alnhan/WearableAlertDevice/Documentation/WAR Feb 22nd-28th.pdf

Executive Summary: This week our team finalized our beginning information for our PDR. We

finished our presentation by completing all required charts, block diagrams, and plans. Our

presentation has been practiced as is ready to go for Monday 3/02. For next week our team will

begin working on schematics and the technical side of our project. At the end of next week we

will have the parts ordered for our project and the schematics done for when the parts arrive. The

software will be continued to be worked on so that we may be completely ready for testing when

the project is finished building.

Hardware:

Cody C.
Progress:
- Found Arduino Nano ESP32 schematics (~ 5 minutes)
- Create block diagram for gunshot detection (~1 hour 30 minutes)
- Presentation:
- Created slides and researched for PDR (~ 4 hours)

■ Created rough script and bullet points on what I need to cover

- Going in detail onto the I2S MEMS microphone, explaining the

functions, restrictions, and how we plan to overcome the

limitations of 140 dB

- Practice PDR presentation individually (~ 30 minutes)
- 2/28 – Weekly meeting with the team (~ 3 hours)
- Finalize what components and features we want to use for the wearable alert

device (Prioritize functionality over portability)

■ Boost converter, power supply

- Practice presentation with the group

■ Muting at correct times, coordinating who will say what information and

at which slides.

Total Hours Worked: ~ 9 Hours 5 Minutes

Future Work/Plan

- 3/2 - Preliminary Design Review (Presentation)
- Finalize order of parts for the gunshot detection and for overall project
- Create schematics for all components
- Reorganize Arduino Nano ESP32 schematics
- Create rough schematics of all required components for the gunshot detection

:

Hardware:

Ryan K.
Progress:
- 2/25 (2hrs)
- Created and worked on hardware specific slides for the PDR
- Created block diagram for the positioning module
- Practiced presenting PDR slides individually
- 2/28 (3hrs)
- Attended team meeting where we discussed and finalized the PDR presentation
- Practice presenting the PDR slides as a group

Total Hours Worked: 5hrs

Future Work/Plan:

- Deliver PDR presentation Monday (3/2)
- Coordinate with team on what all needs to be ordered for the project
- Create schematics for all components

Software:

Alex H.
Progress:

Total Hours Worked:

- 2/24 (1 h 27 min)
- Continued working on PDR slides
- Finished introduction slide for PDR
- Finished audio processing software block diagram
- 2/27 (3 h 52 min)
- Completed PDR slides
- Finished overall software block diagram
- Practiced presenting software slides of PDR
- 2/28 (2 h)
- Practiced entire PDR presentation with the rest of the team

Future Work/Plan:

- Deliver PDR presentation Monday (3/2) night
- Start writing software for device

Project Manager:

Jonas W.

Progress:

- 2/24 (30 min)
- Began work on PDR slides
- Finished introduction slide for PDR
- 2/27 (1 hr)
- Finished my PDR slides
- Finished block diagrams and budget plan
- Finished Datasheet booklet
- 2/28 (2 h)
- Practiced entire PDR presentation with the rest of the team
- Finalized PDR with charts and information

Total Hours Worked: 3 hr 30 min

Future Work/Plan:

- Deliver PDR
- Order parts for circuit
- Finish schematics for hardware and begin slides for CDR
