alnhan/WearableAlertDevice/Presentations/CCEW PDR.pdf

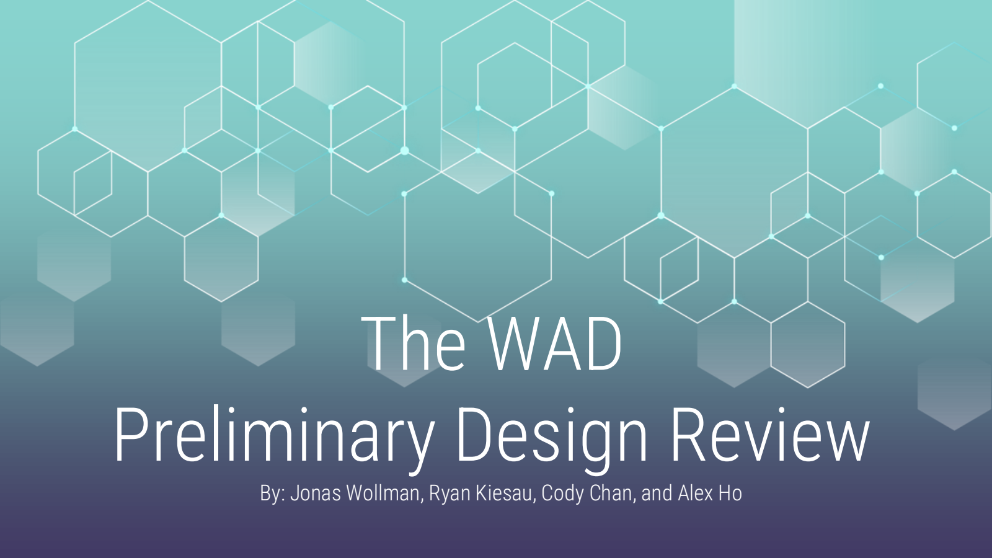
[picture p57: page 1]

# The WAD Preliminary Design Review

By: Jonas Wollman, Ryan Kiesau, Cody Chan, and Alex Ho

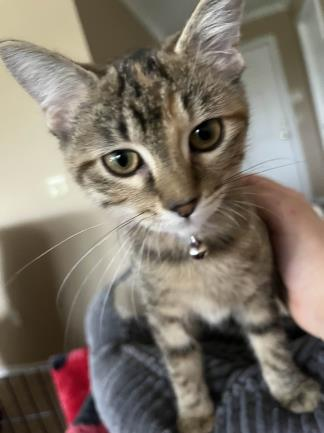
[picture p58: figure]

# Introductions

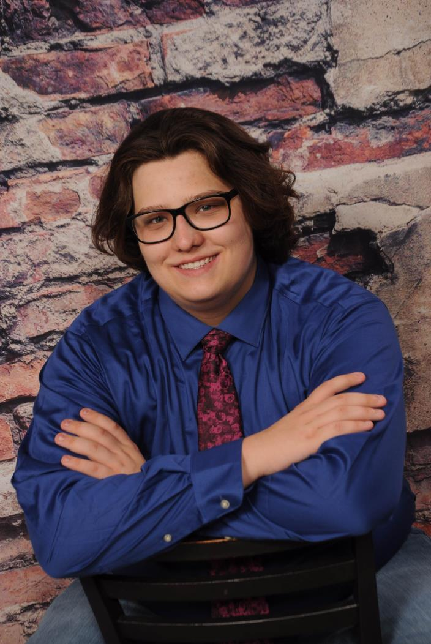
[picture p59: figure]

### Name: Jonas Wollman

### Major: Computer Engineering

### Role: Project Manager

### Post-College Plans: Working as an electronics engineer for the 76th Software Engineering Group (555th Squadron) at Tinker Air Force Base

JW

RK

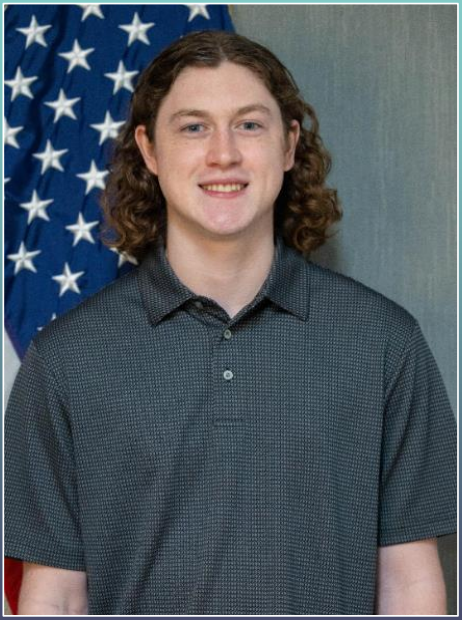
[picture p60: figure]

### Name: Ryan Kiesau

### Major: Electrical Engineering

### Role: Hardware

### Post-College Plans: Working as an electronics engineer for the 76th Software Engineering Group (557th Squadron) at Tinker Air Force Base

# Introductions

CC

# Introductions

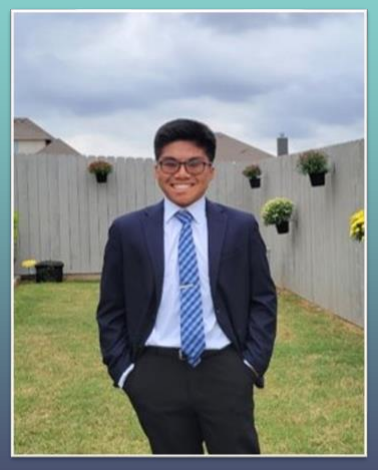
[picture p61: figure]

### Name: Cody Chan

### Major: Computer Engineering

### Role: Hardware

### Post-College Plans: Pursue Master’s in Electrical Engineering -The University of Oklahoma

AH

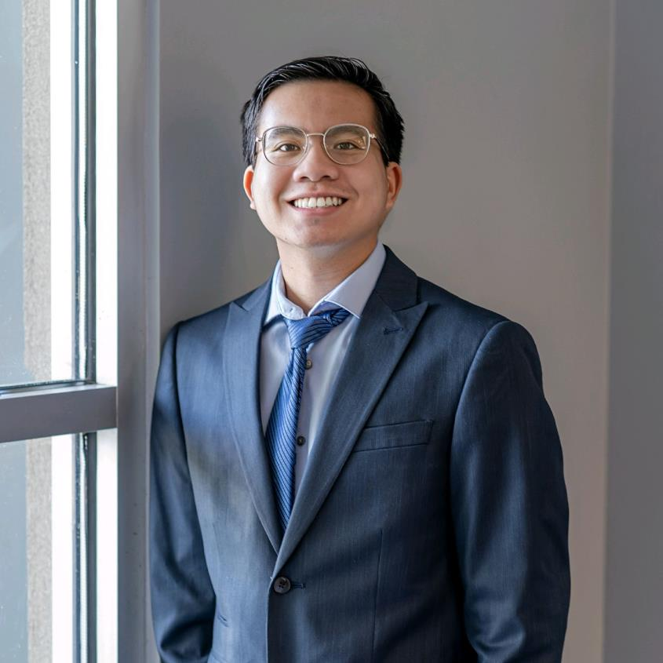
[picture p62: figure]

Name: Alex Ho

Major: Computer Engineering

Graduation Date: May 2026

Role: Software

Post-College Plans: Working as an electronics engineer at Tinker Air Force Base

# Introductions

# Problem & Plan

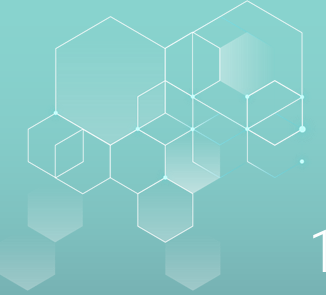
[picture p63: figure]
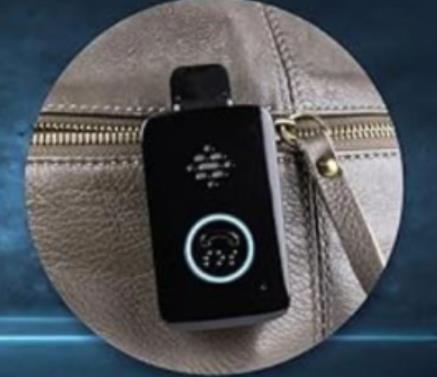
[picture p64: figure]

# 1. Wearability

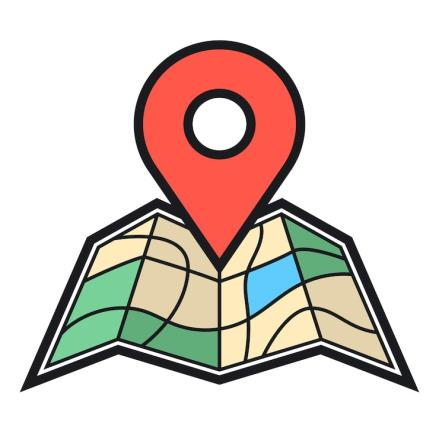
[picture p65: figure]

# 2. Functionality

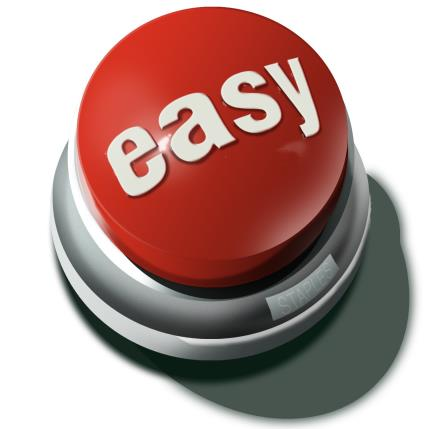
[picture p66: figure]

# 3. Ease of Use

JW

# Problem & Plan

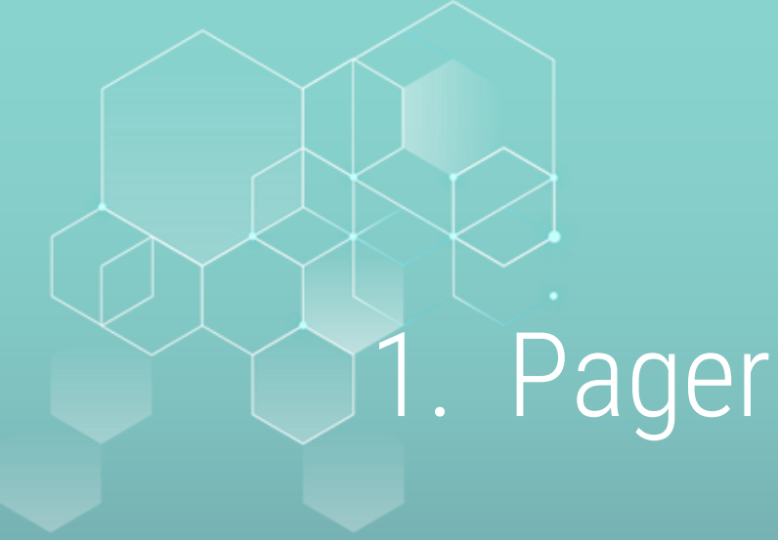
[picture p67: figure]
1. Pager
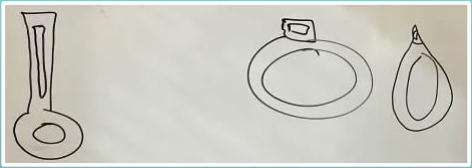
[picture p68: figure]

# 2. Gunshot & GPS

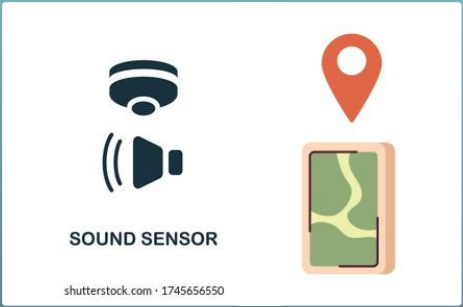
[picture p69: figure]
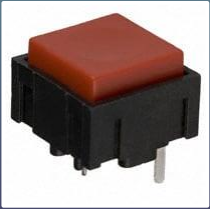
[picture p70: figure]

# 3. Click of a Button

JW

# Overview Block Diagram

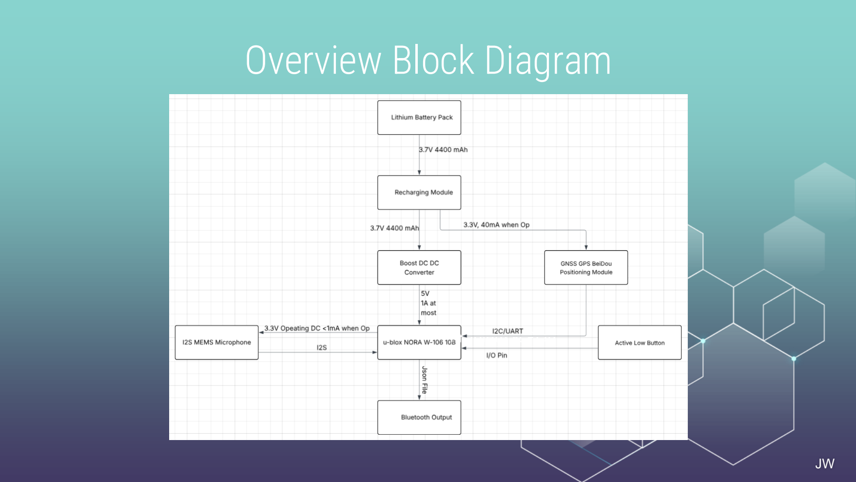
[picture p71: page 8]

JW

# Hardware System Overview

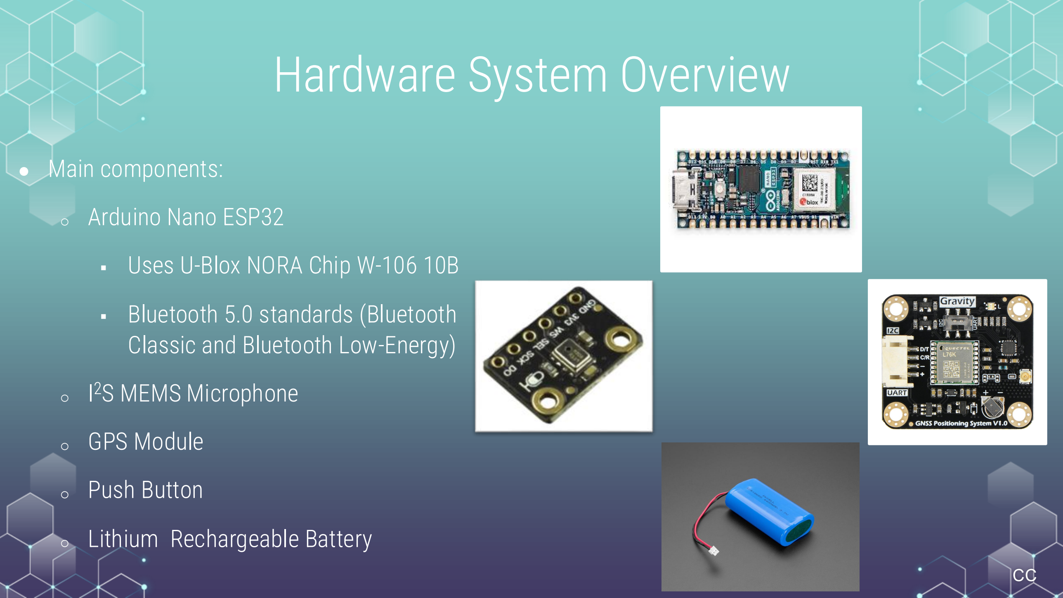
[picture p72: page 9]

- Main components:
- Arduino Nano ESP32
- Uses U-Blox NORA Chip W-106 10B
- Bluetooth 5.0 standards (Bluetooth Classic and Bluetooth Low-Energy)
- I

2S MEMS Microphone

- GPS Module
- Push Button
- Lithium Rechargeable Battery

CC

# Audio Sampling Block Diagram

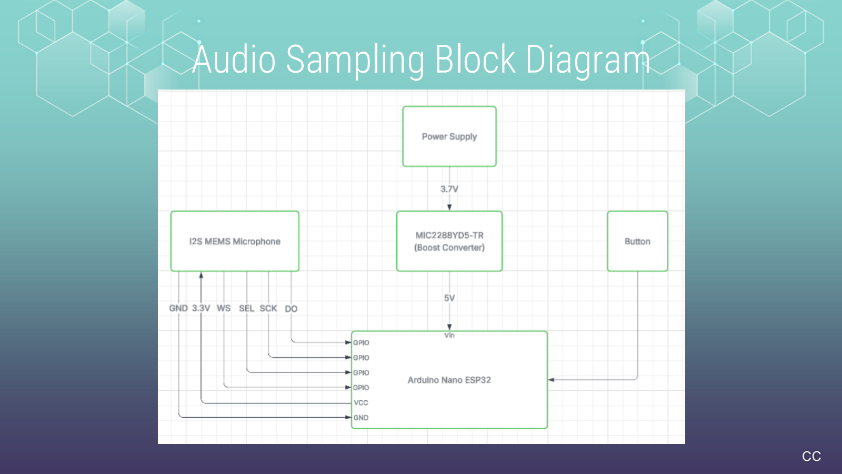
[picture p73: page 10]

CC

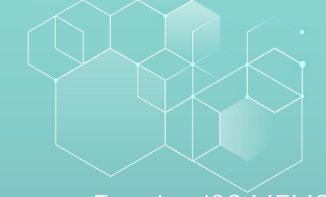
[picture p74: figure]
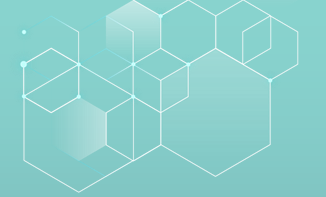
[picture p75: figure]

- Fermion I2S MEMS Microphone
- Operating Voltage: 3.3V
- Low Current: < 1mA
- Sound Pressure Level: 140 dB
- Signal-to-Noise Ratio: 59 dB
- Supports I²S

CC

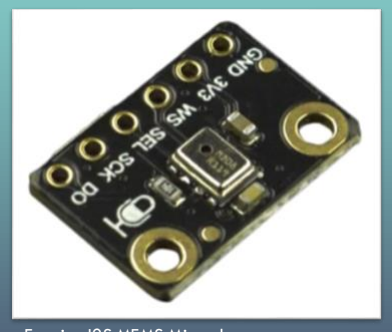
[picture p76: figure]

Fermion I2S MEMS Microphone

# Microphone Hardware

# Positioning Block Diagram

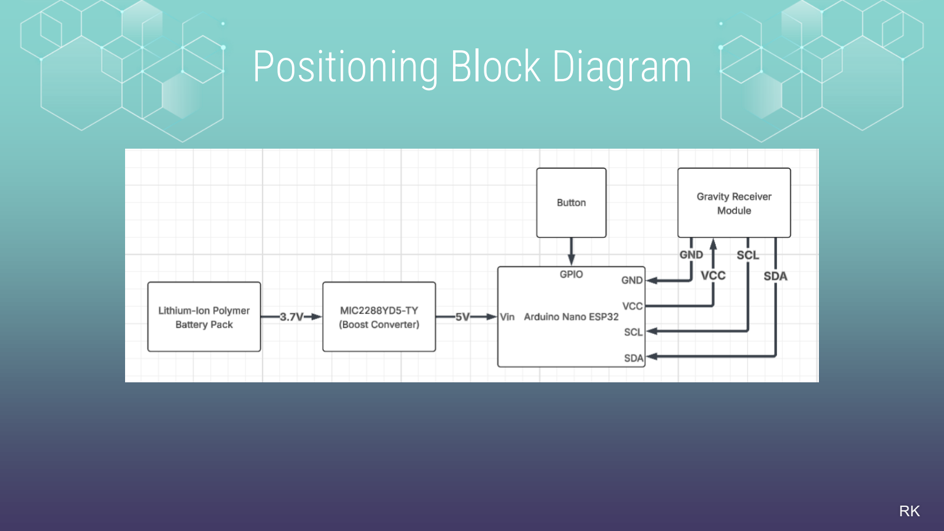
[picture p77: page 12]

RK

# Positioning Hardware

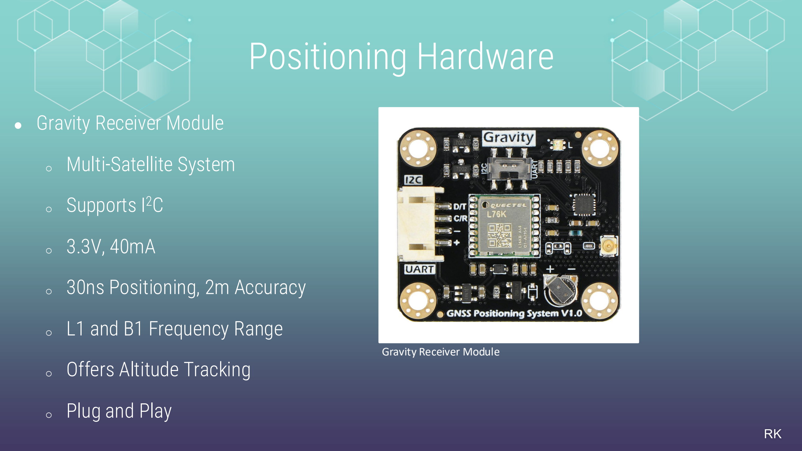
[picture p78: page 13]

- Gravity Receiver Module
- Multi-Satellite System
- Supports I²C
- 3.3V, 40mA
- 30ns Positioning, 2m Accuracy
- L1 and B1 Frequency Range
- Offers Altitude Tracking
- Plug and Play

Gravity Receiver Module

RK

# Power Supply

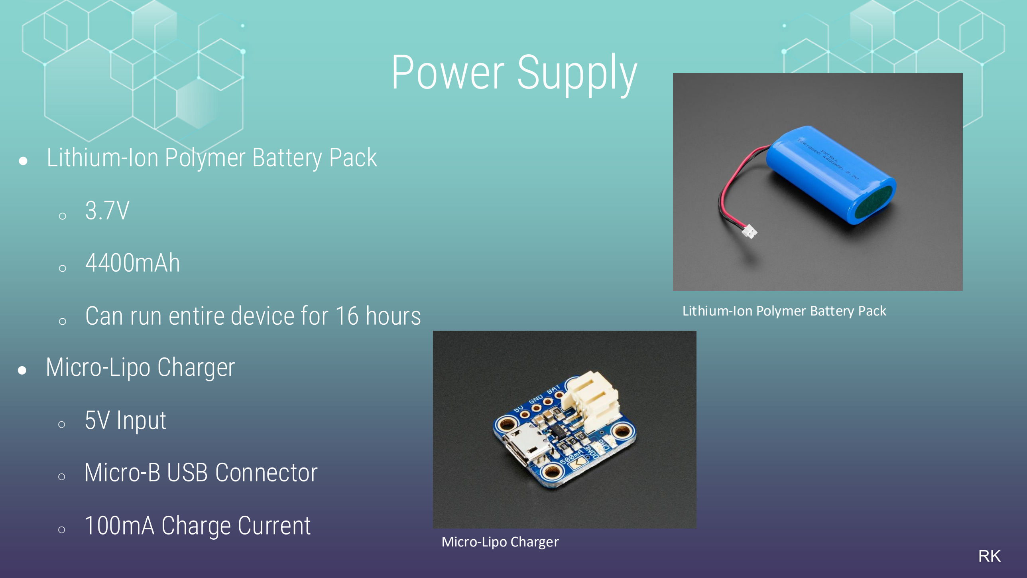
[picture p79: page 14]

- Lithium-Ion Polymer Battery Pack
- 3.7V
- 4400mAh
- Can run entire device for 16 hours

RK

Lithium-Ion Polymer Battery Pack

Micro-Lipo Charger

- Micro-Lipo Charger
- 5V Input
- Micro-B USB Connector
- 100mA Charge Current

Overview of Implementation

Programming Language: C++11 (follows joint technical standard ISO¹

/IEC² 14882)

Main Functionality:
1. Collect audio samples and process to find gunshots
2. Collect GPS data
3. Package data and transmit to mobile app

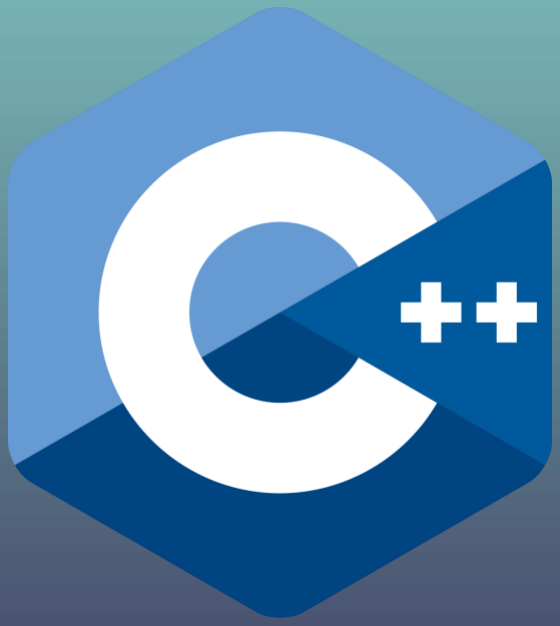
[picture p80: figure]

1. ISO – International Organization for Standardization | AH
2. IEC – International Electrotechnical Commission

# Software Design

Audio Signal Collection
- Data received from microphone in digital PCM¹ format
- I

2S protocol to sample audio from microphone
- Sampling Rate: 44.1 kHz

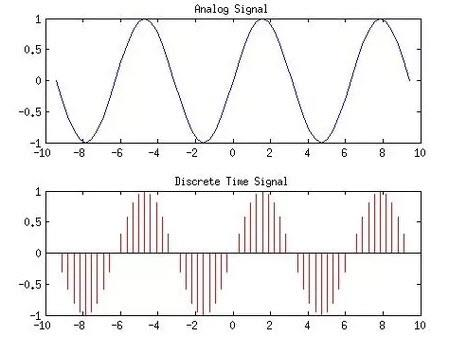
[picture p81: figure]

- Standard frequency for recreating audio signal with the same quality
- ESP32 supports sampling PCM¹ audio at up to 100 kHz
- ESP32 has enough memory to hold large set of audio data (512 KB of SRAM memory)

AH

# Software Design

### 1. PCM - Pulse-Code Modulation

Audio Signal Processing
- Analyzing audio sample with respect to frequency rather than time gives more information on gunshot audio patterns
- Software Library: arduinoFFT by @kosme on GitHub
- Aiming for at least 75% accuracy with gunshot detection

AH

# Signal Processing Design

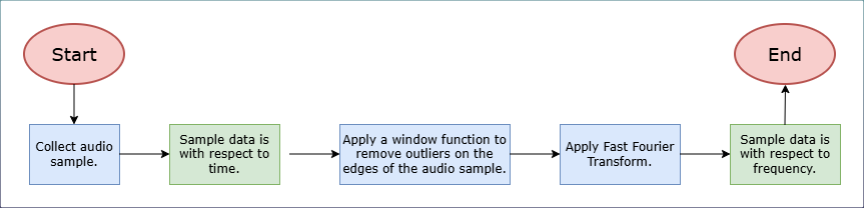
[picture p82: figure]

GPS Data Processing

- Obtains GPS data using I²C (Inter-Integrated Circuit) protocol
- Sampling Rate: 1 Hz

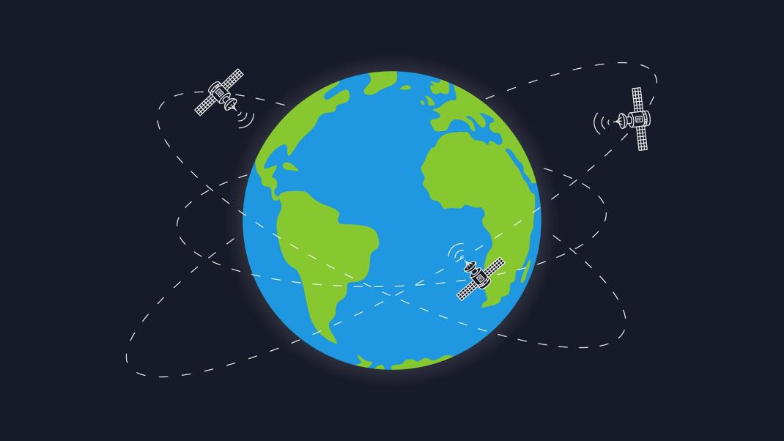
[picture p83: figure]

Collected Data:

1. Timestamp (CST)
2. Latitude (degrees)
3. Longitude (degrees)

AH

# GPS Data Processing

Wireless Data Transmission
- Audio and GPS data will be packaged together in JSON file and transmitted via Bluetooth Low-Energy (BLE)

Testing:
- Since mobile app is not functional yet, data will be transmitted to a completely

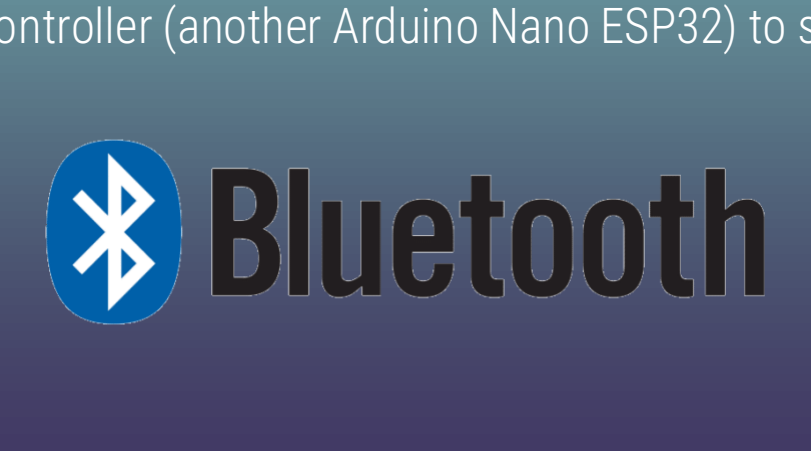
[picture p84: figure]

different microcontroller (another Arduino Nano ESP32) to see if transmission is successful

AH

# Bluetooth Design

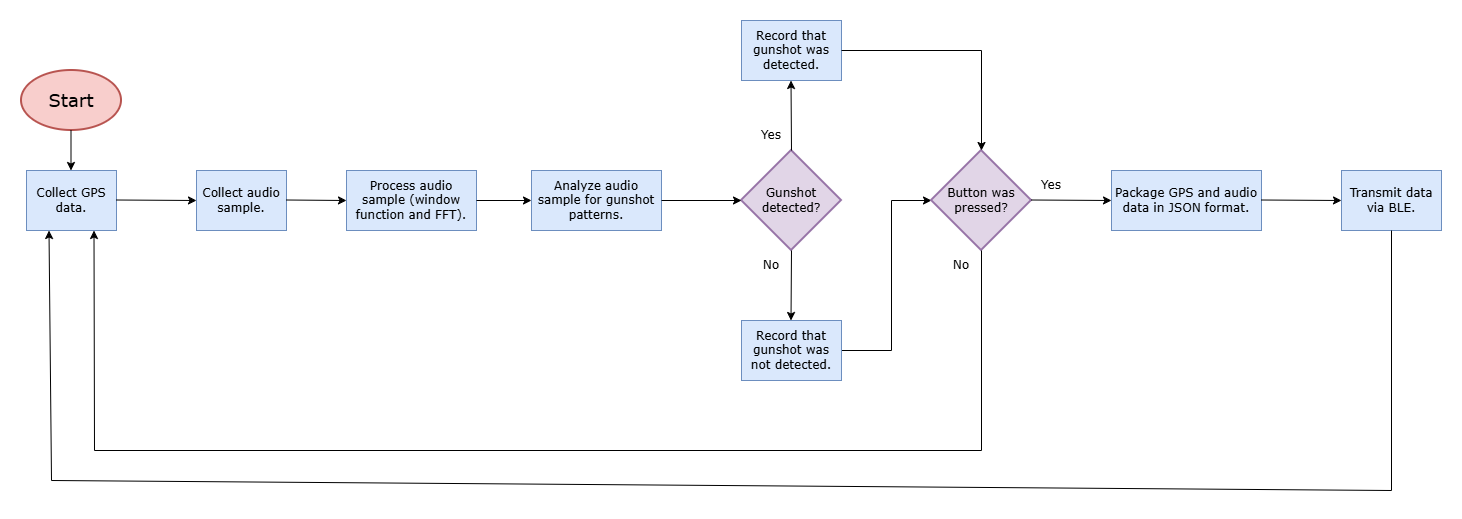
[picture p85: figure]

AH

# Software Block Diagram

# Budget Plan

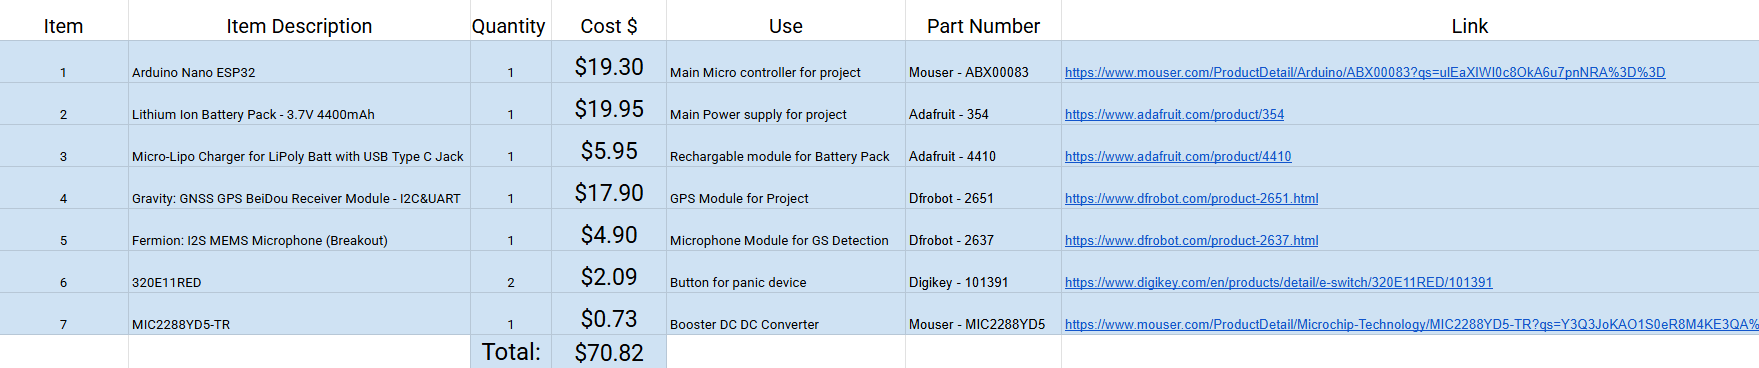
[picture p86: figure]

JW

JW

# Upcoming Plans

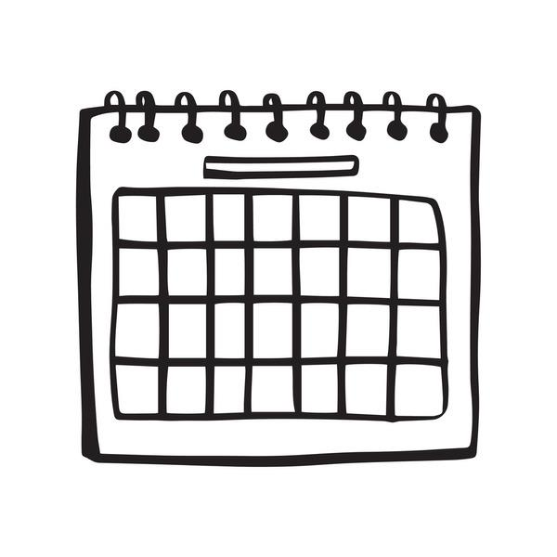
[picture p87: figure]

1-2 Weeks from Today:

-Ordering Parts & Creation of Schematics

2-4 Weeks from Today:

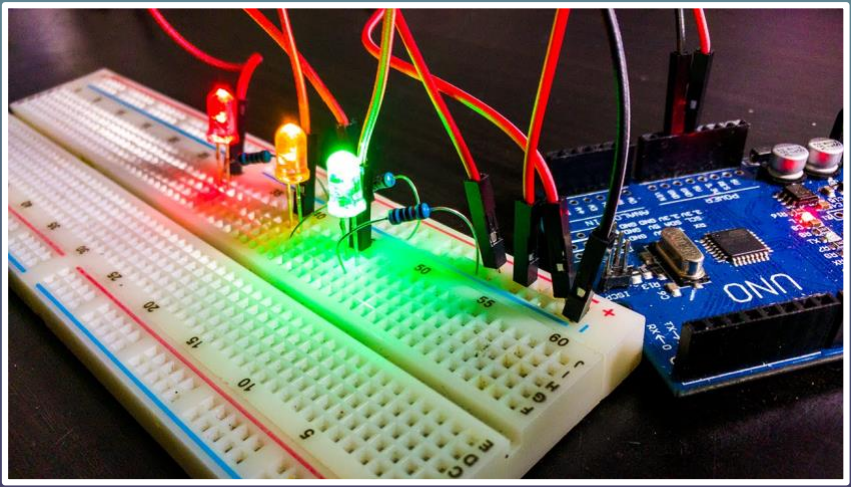
[picture p88: figure]

-Building of Board & Debugging

4-8 Weeks from Today:

-Testing & Future Planning

# Questions?
