alnhan/WearableAlertDevice/Documentation/Testing Images/20260425_123621.jpg

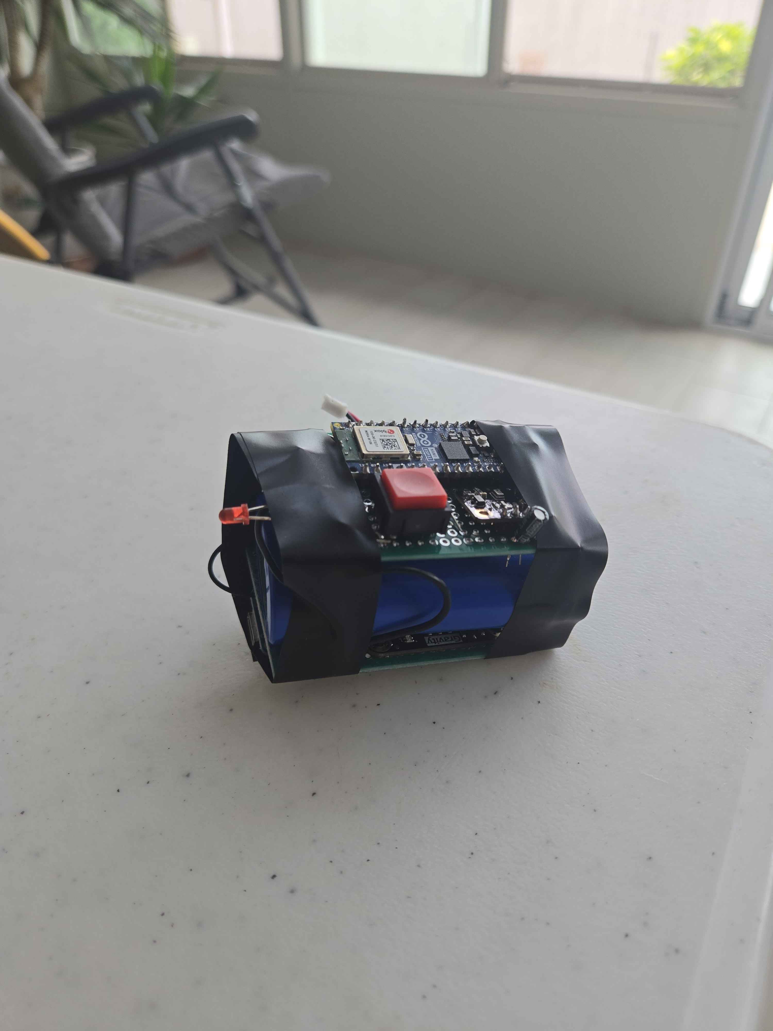
Documentation/Testing Images/20260425_123621.jpg
