alnhan/WearableAlertDevice/Documentation/Testing Images/20260425_123703.jpg

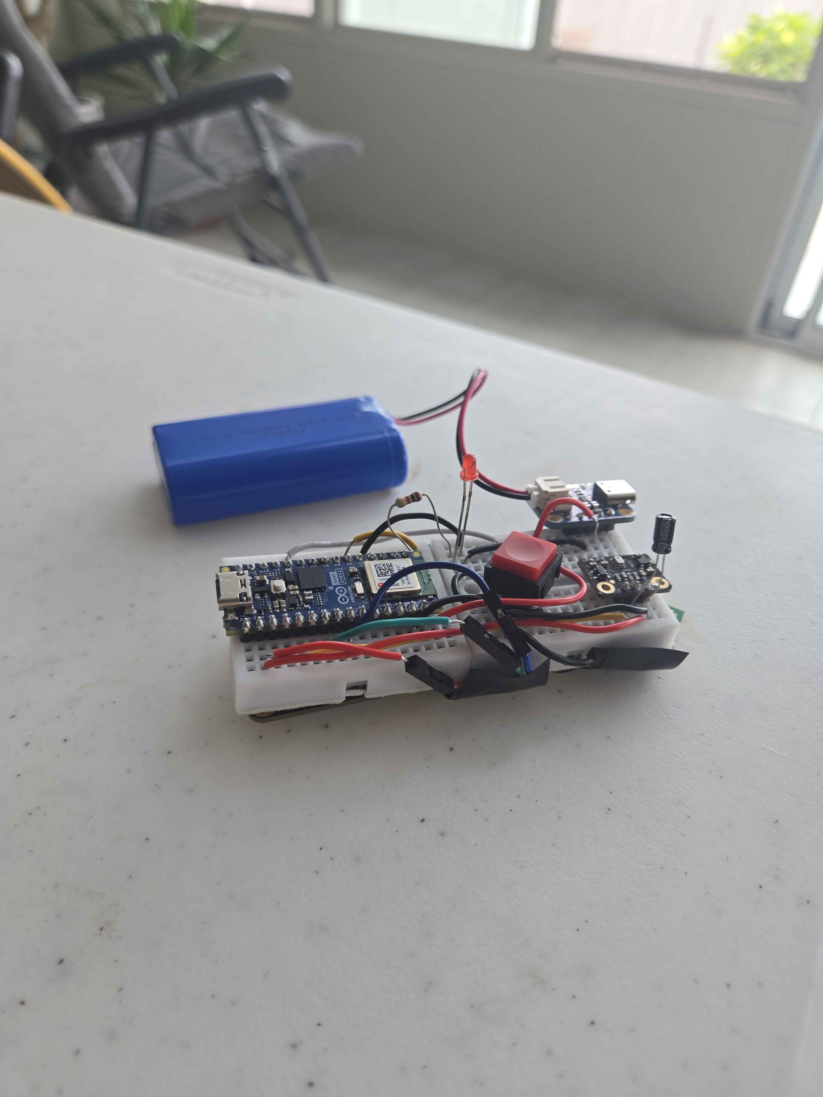
Documentation/Testing Images/20260425_123703.jpg
