alnhan/WearableAlertDevice/Documentation/Testing Images/20260425_123842.jpg

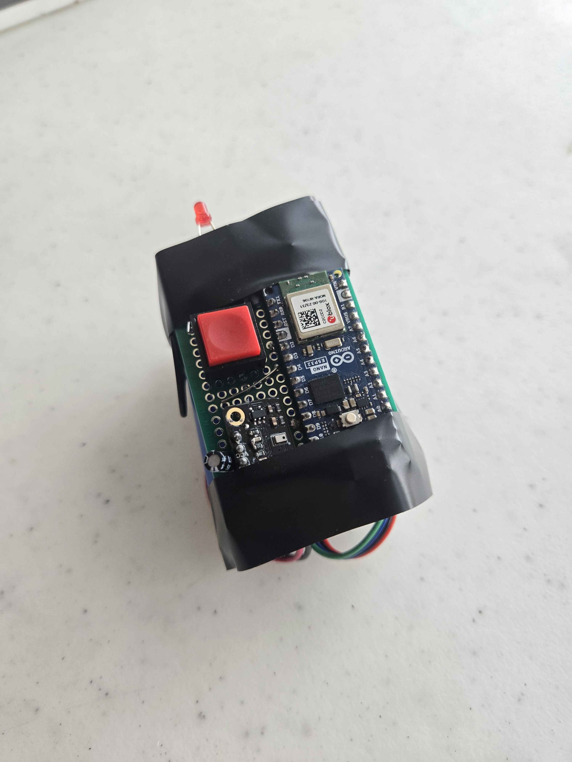
Documentation/Testing Images/20260425_123842.jpg
