alnhan/WearableAlertDevice/Documentation/Testing Images/20260425_123859.jpg

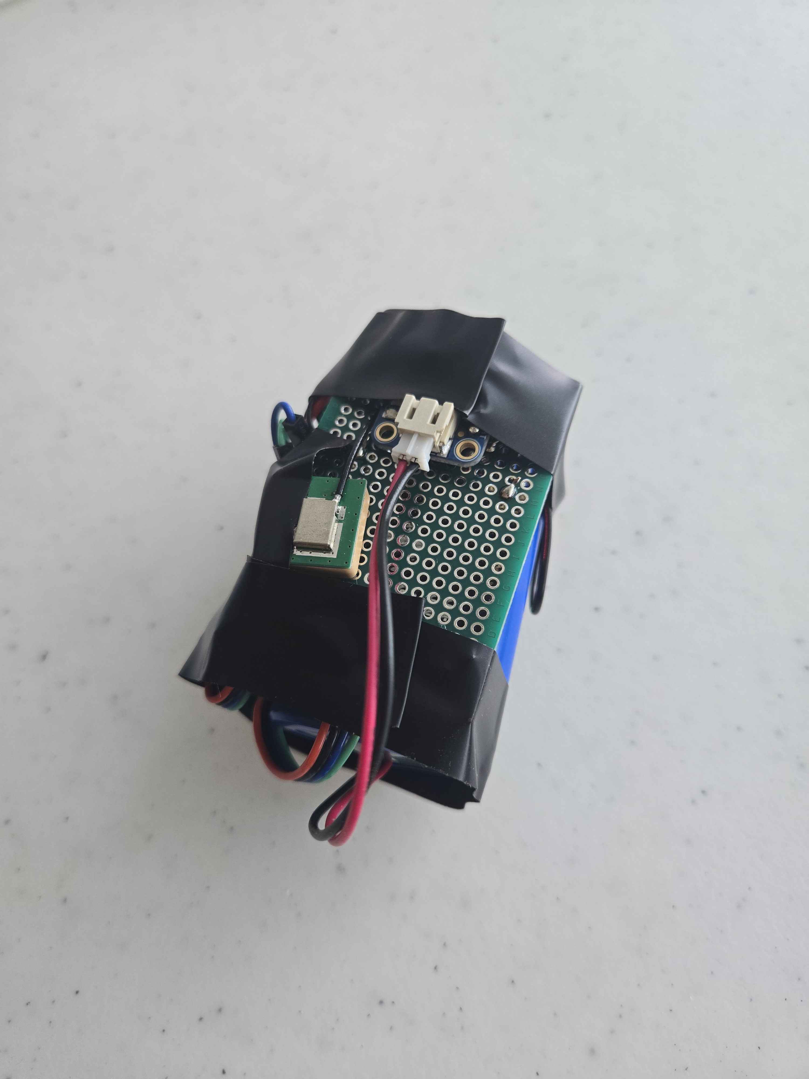
Documentation/Testing Images/20260425_123859.jpg
