alnhan/WearableAlertDevice/Documentation/Testing Images/20260425_124032.jpg

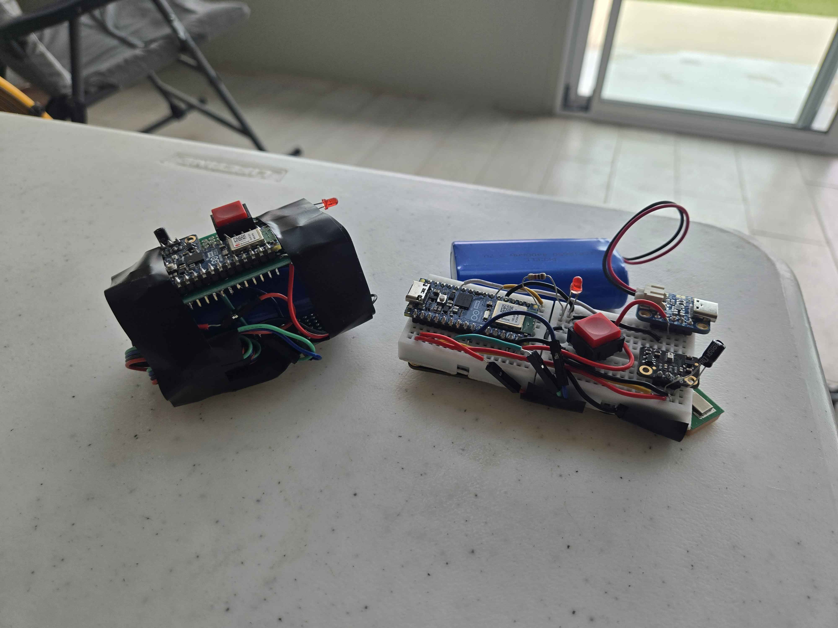
Documentation/Testing Images/20260425_124032.jpg
