alnhan/WearableAlertDevice/Documentation/Testing Images/IMG_0361.jpg

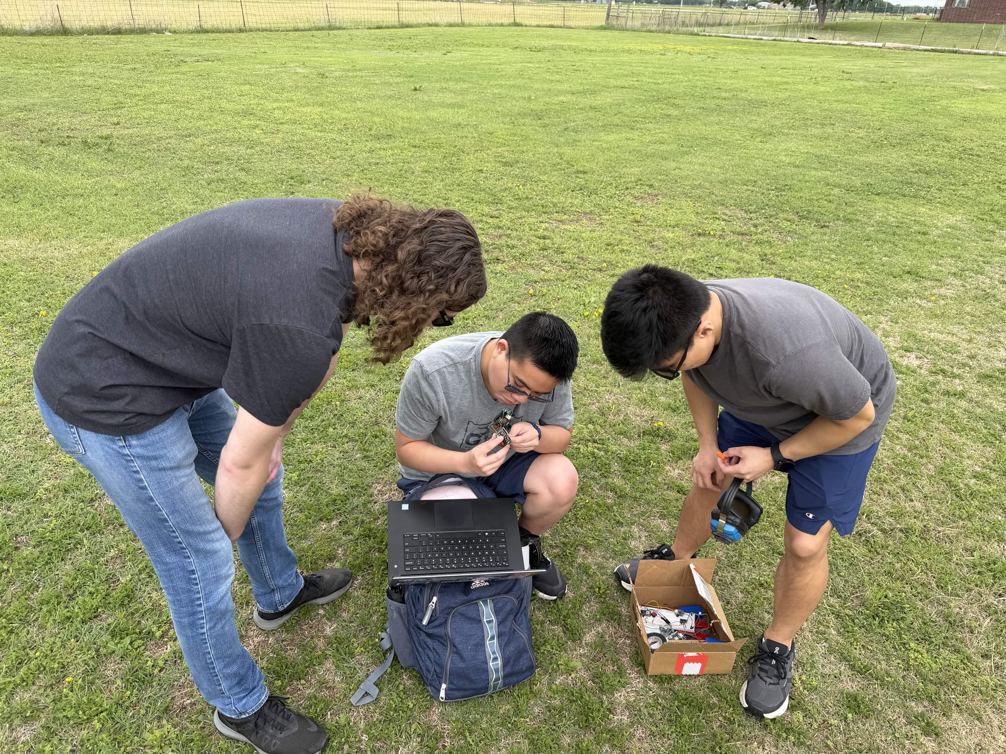
Documentation/Testing Images/IMG_0361.jpg
