alnhan/WearableAlertDevice/Documentation/Testing Images/IMG_0362.jpg

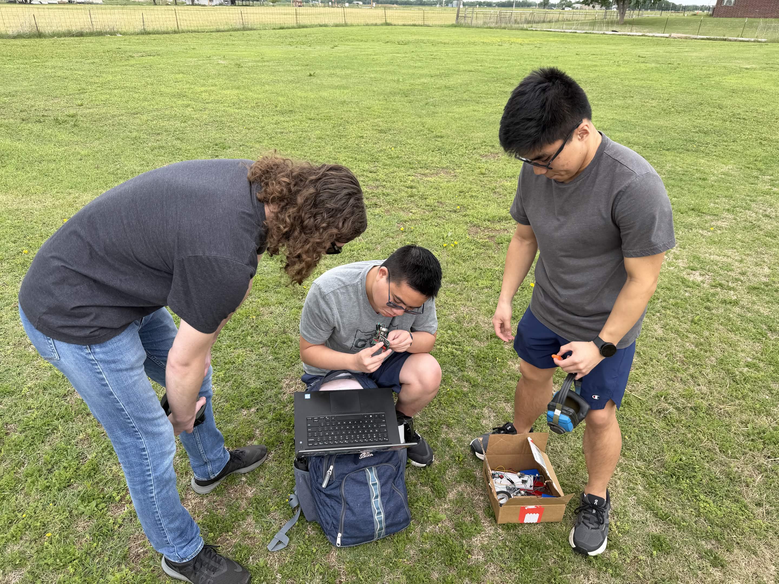
Documentation/Testing Images/IMG_0362.jpg
