alnhan/WearableAlertDevice/Documentation/Testing Images/IMG_0363.jpg

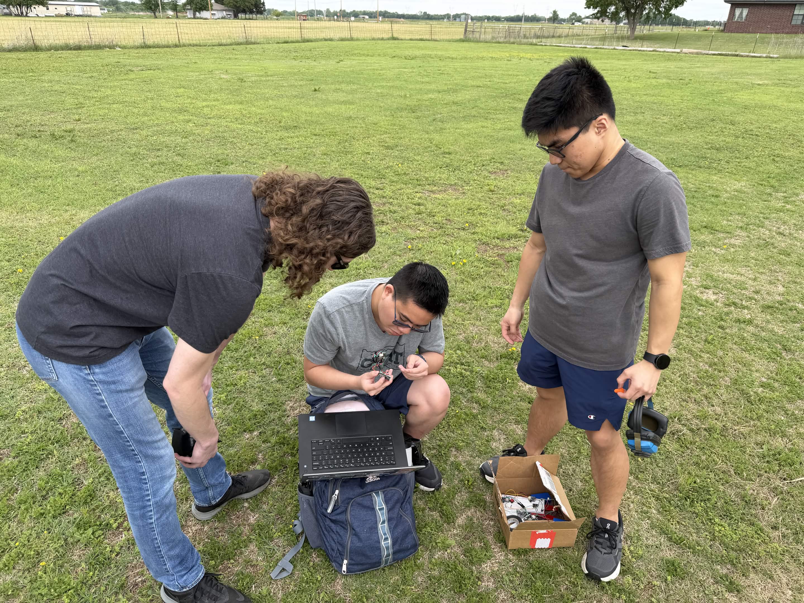
Documentation/Testing Images/IMG_0363.jpg
