alnhan/WearableAlertDevice/Gunshot Detection Files/Fermion - MEMS Microphone Resources/SEN0487_mems-microphone-sensor_dimension_V1.0.pdf

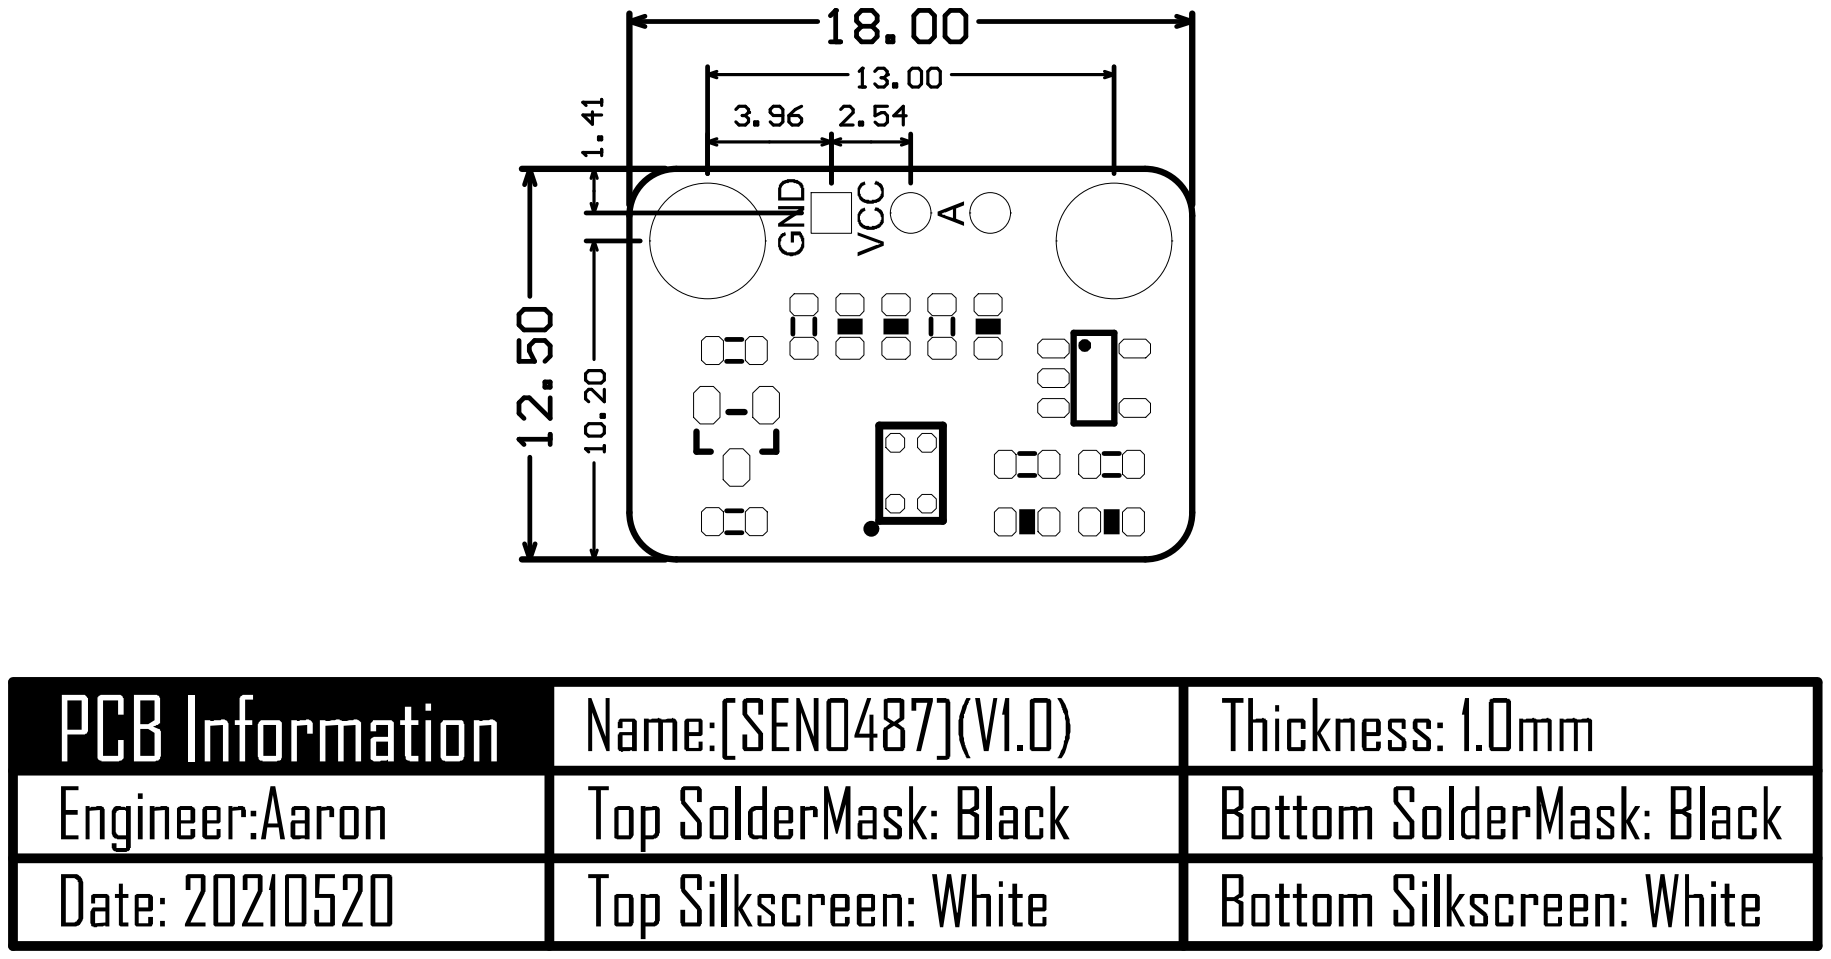
[picture p116: page 1]
