alnhan/WearableAlertDevice/Gunshot Detection Files/Old Microphone/I2S Microphone Resources/SEN0526_i2s-mems-microphone_schematics_v1.0.pdf

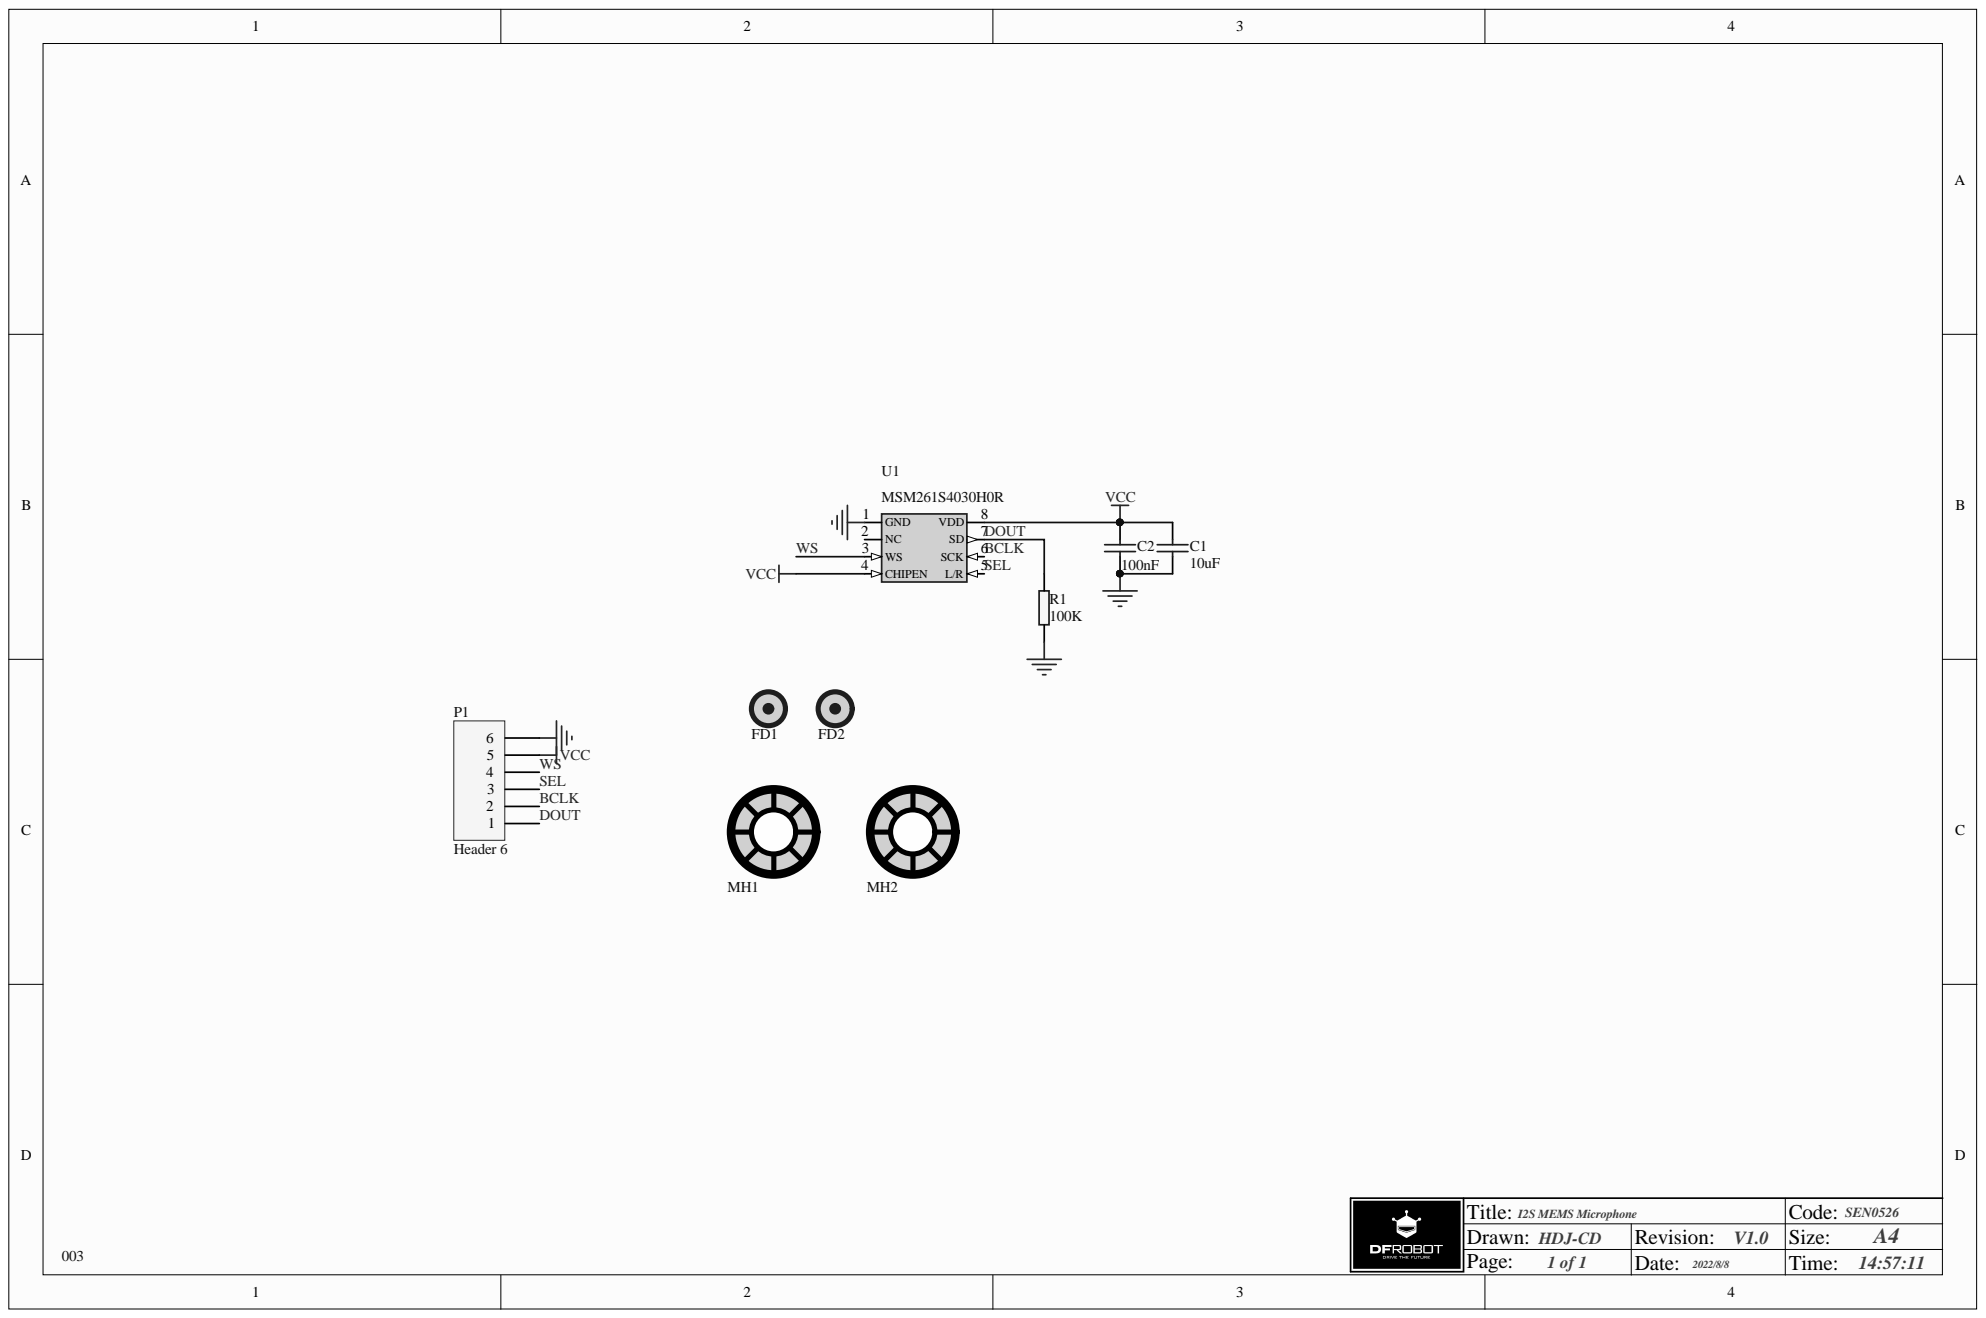
[picture p117: page 1]

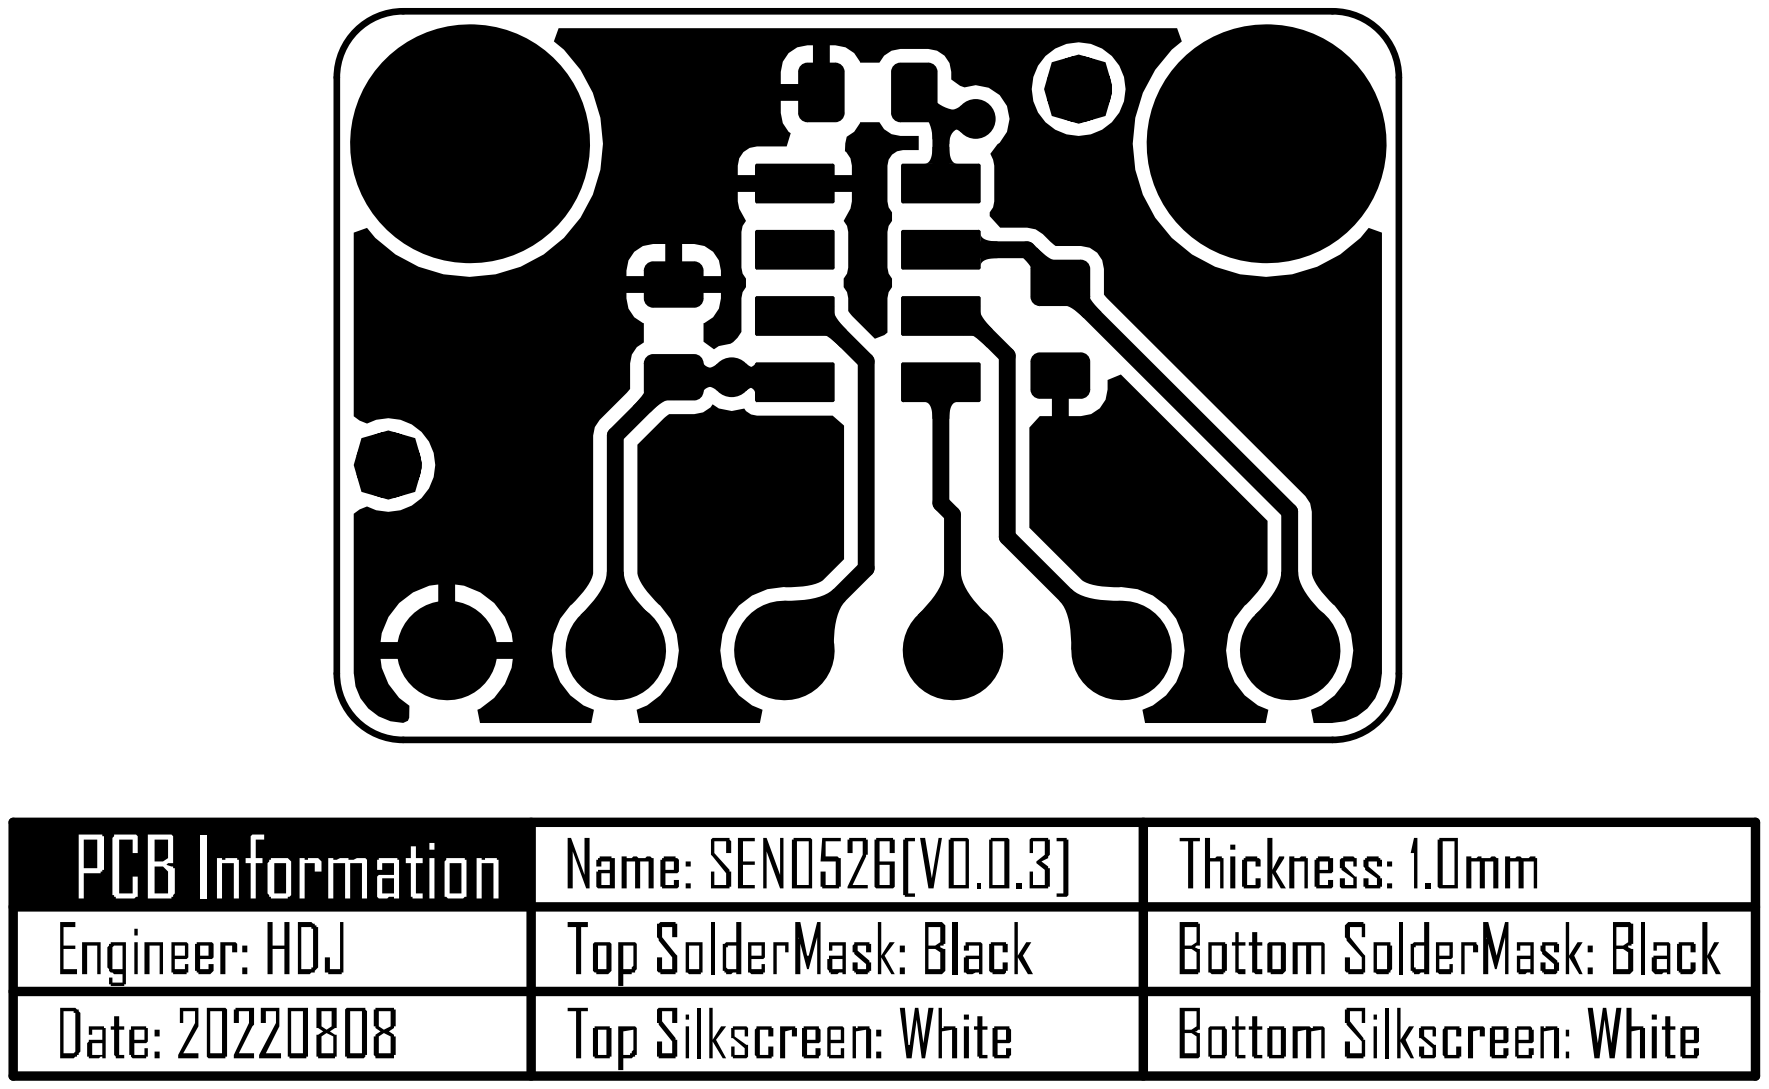
[picture p118: page 2]

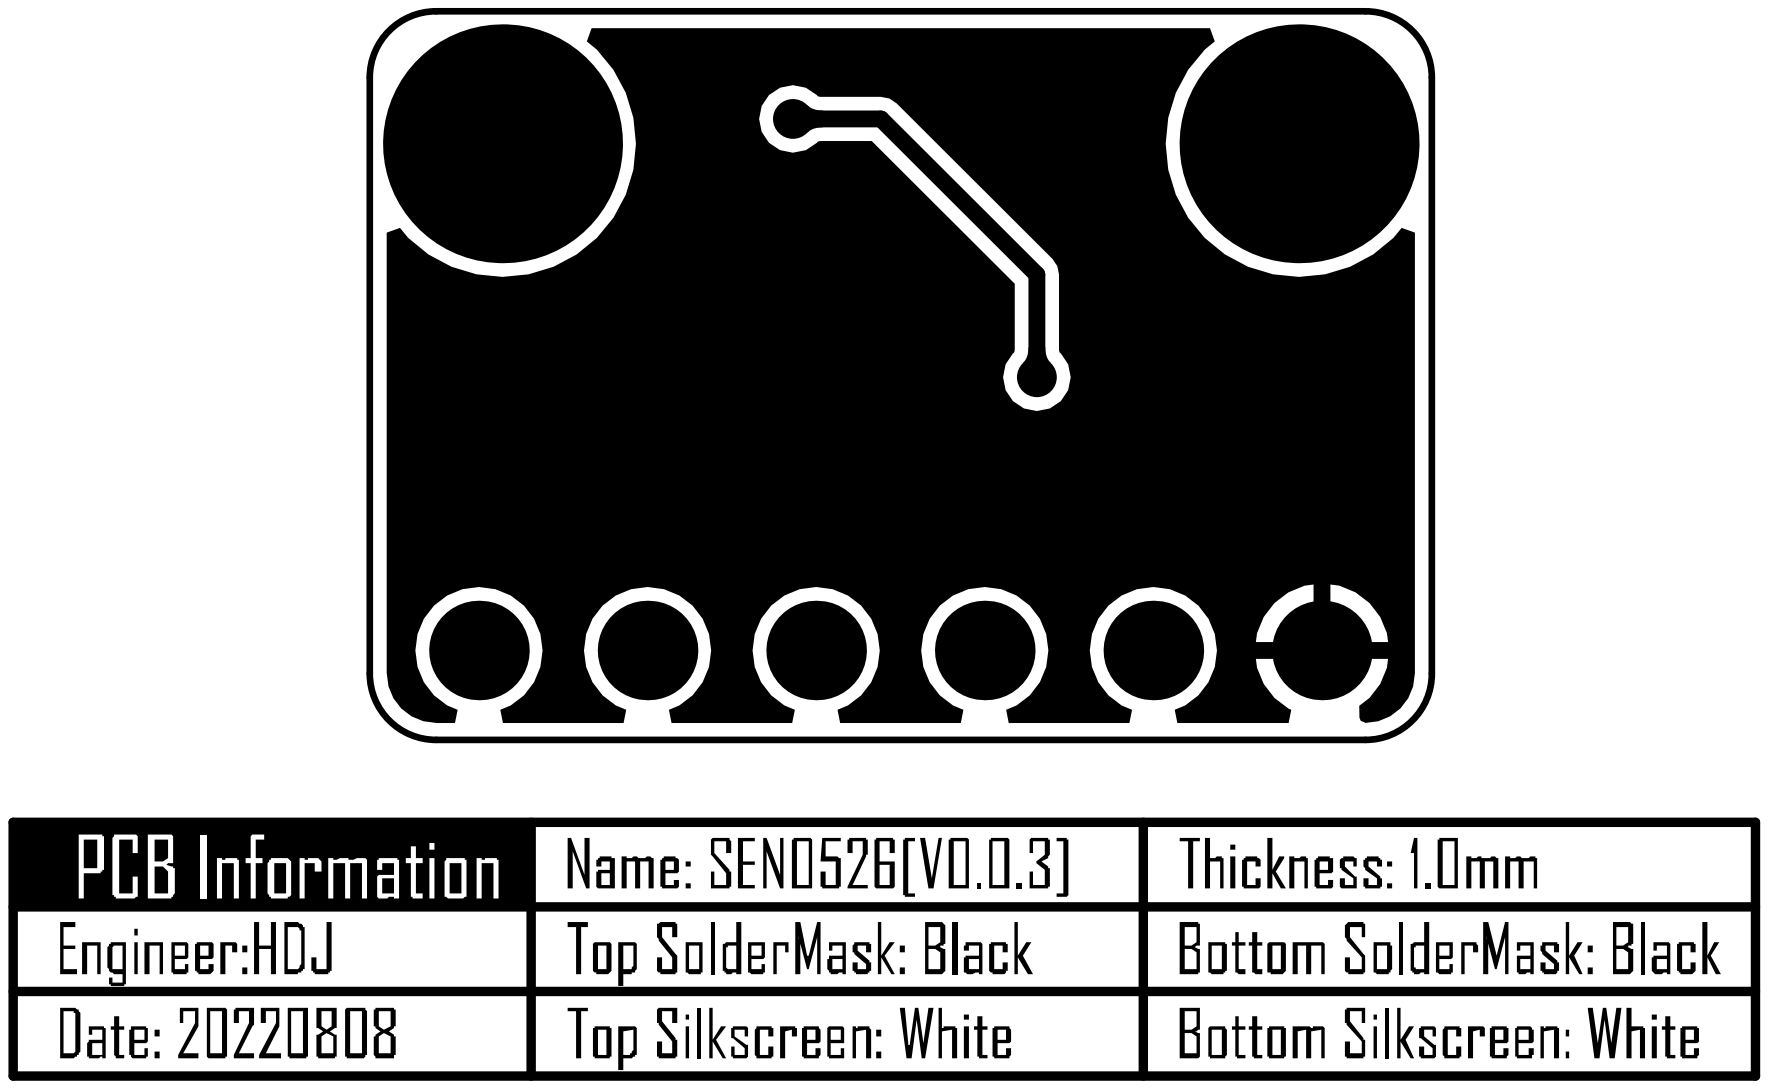
[picture p119: page 3]

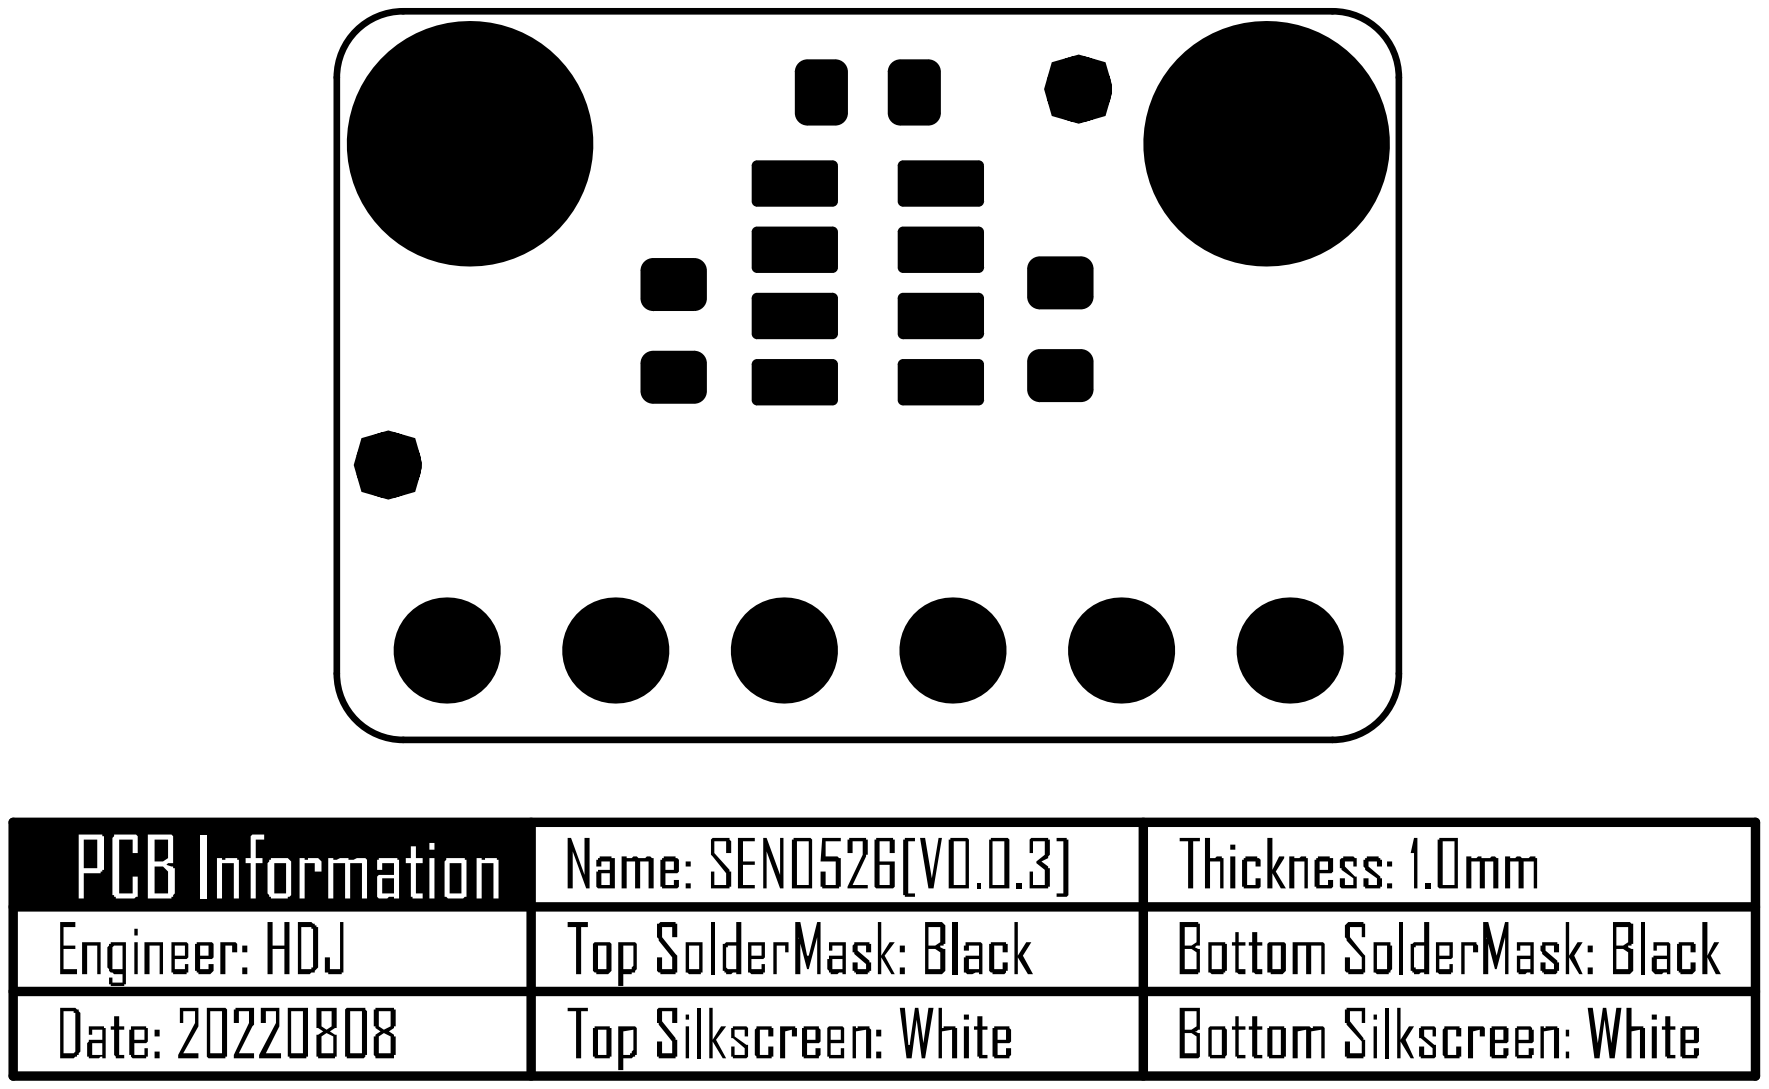
[picture p120: page 4]

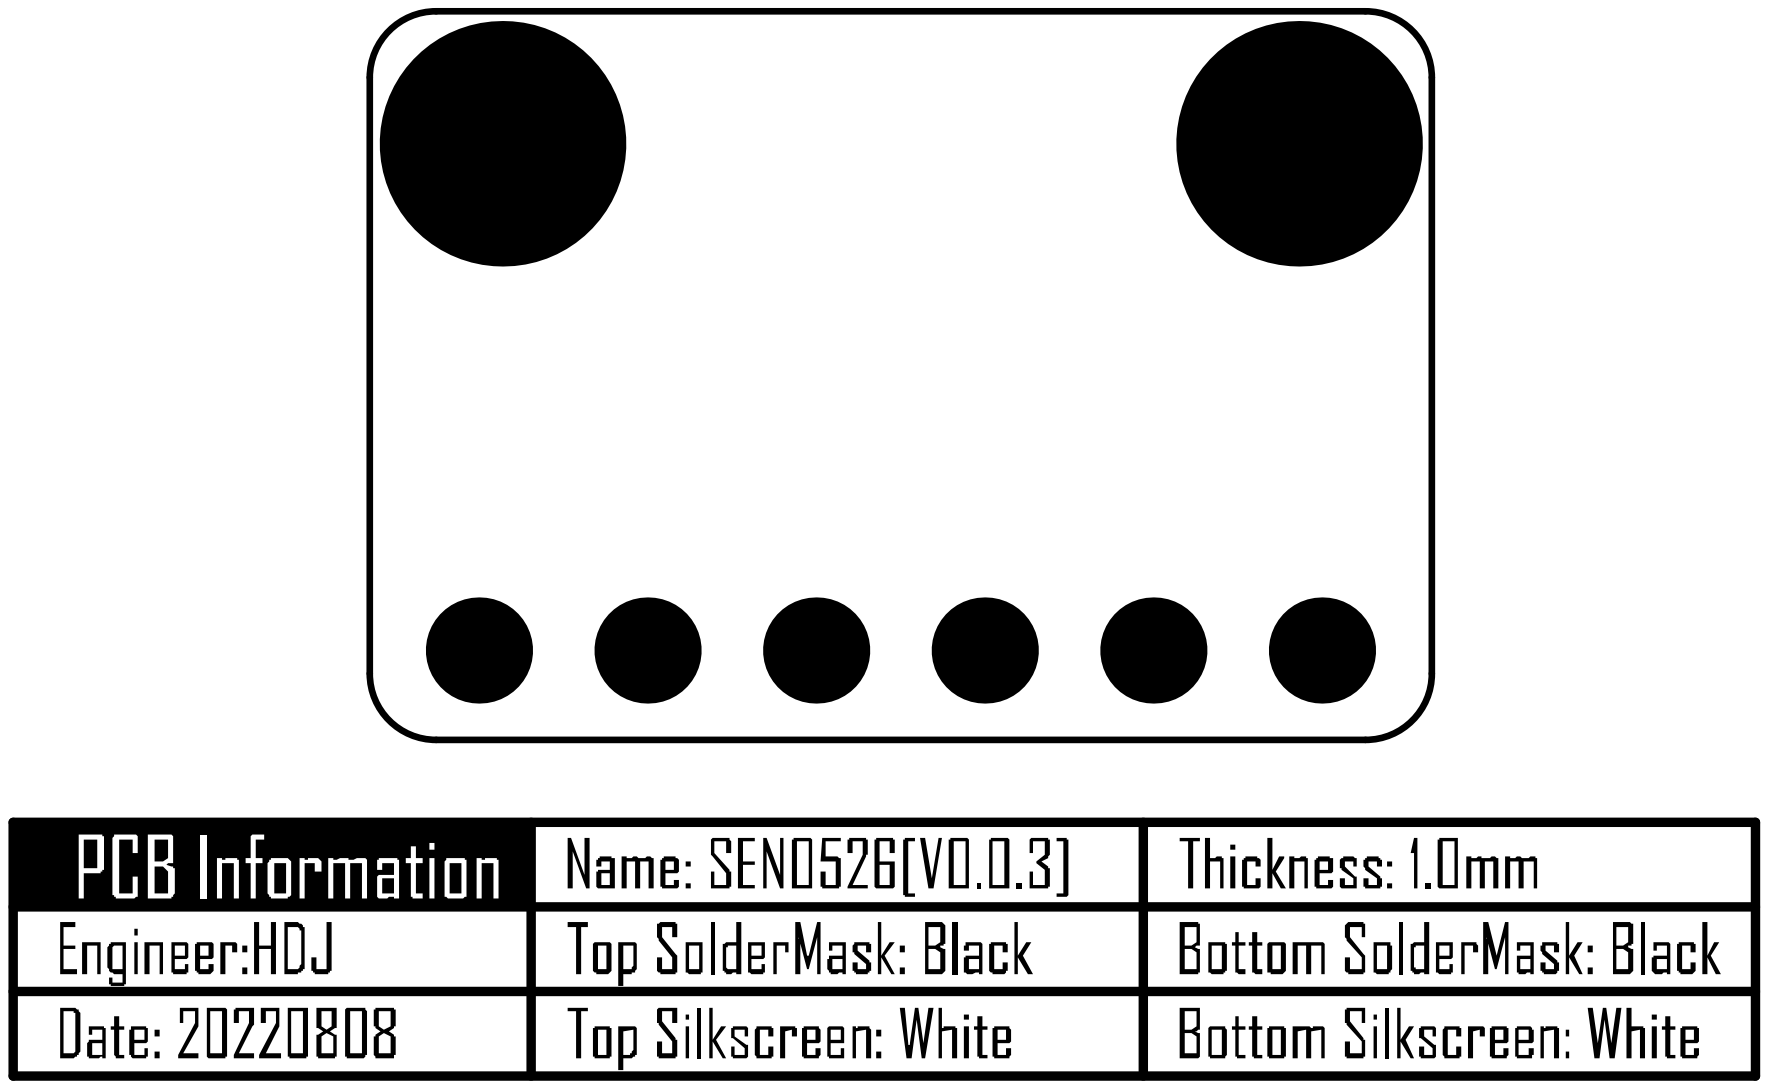
[picture p121: page 5]

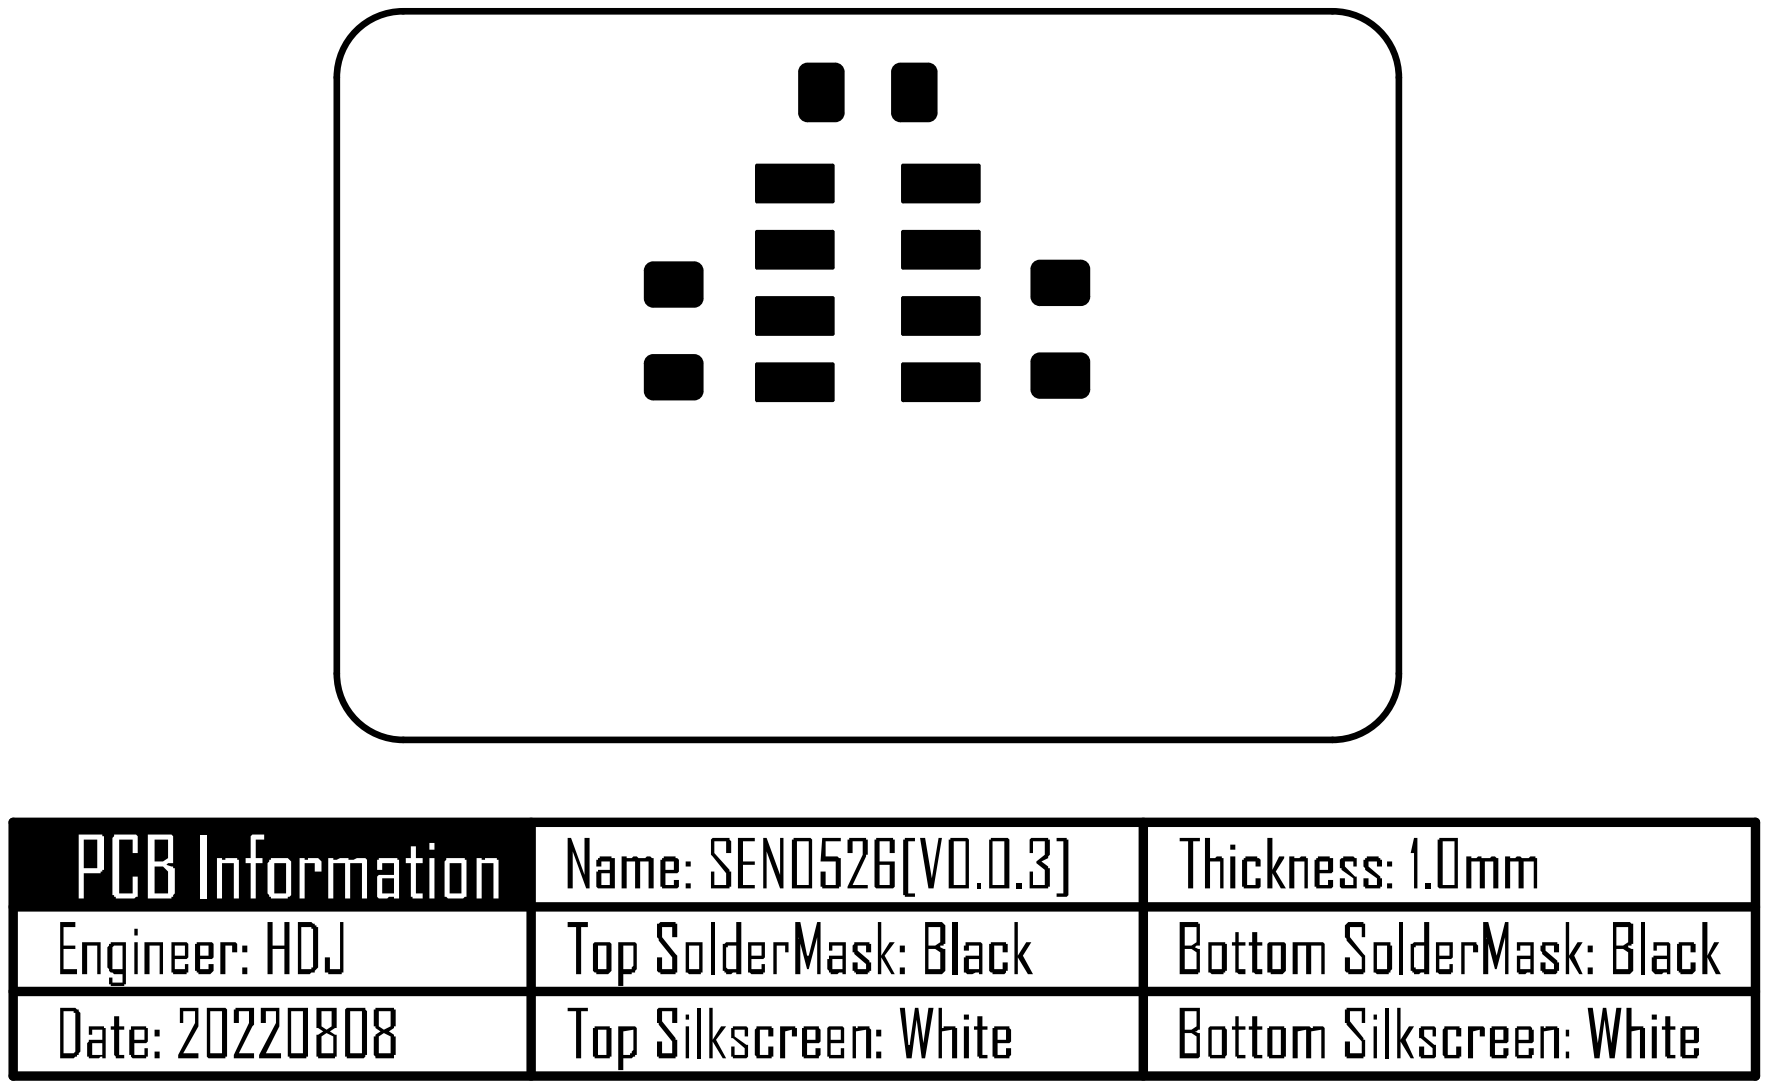
[picture p122: page 6]

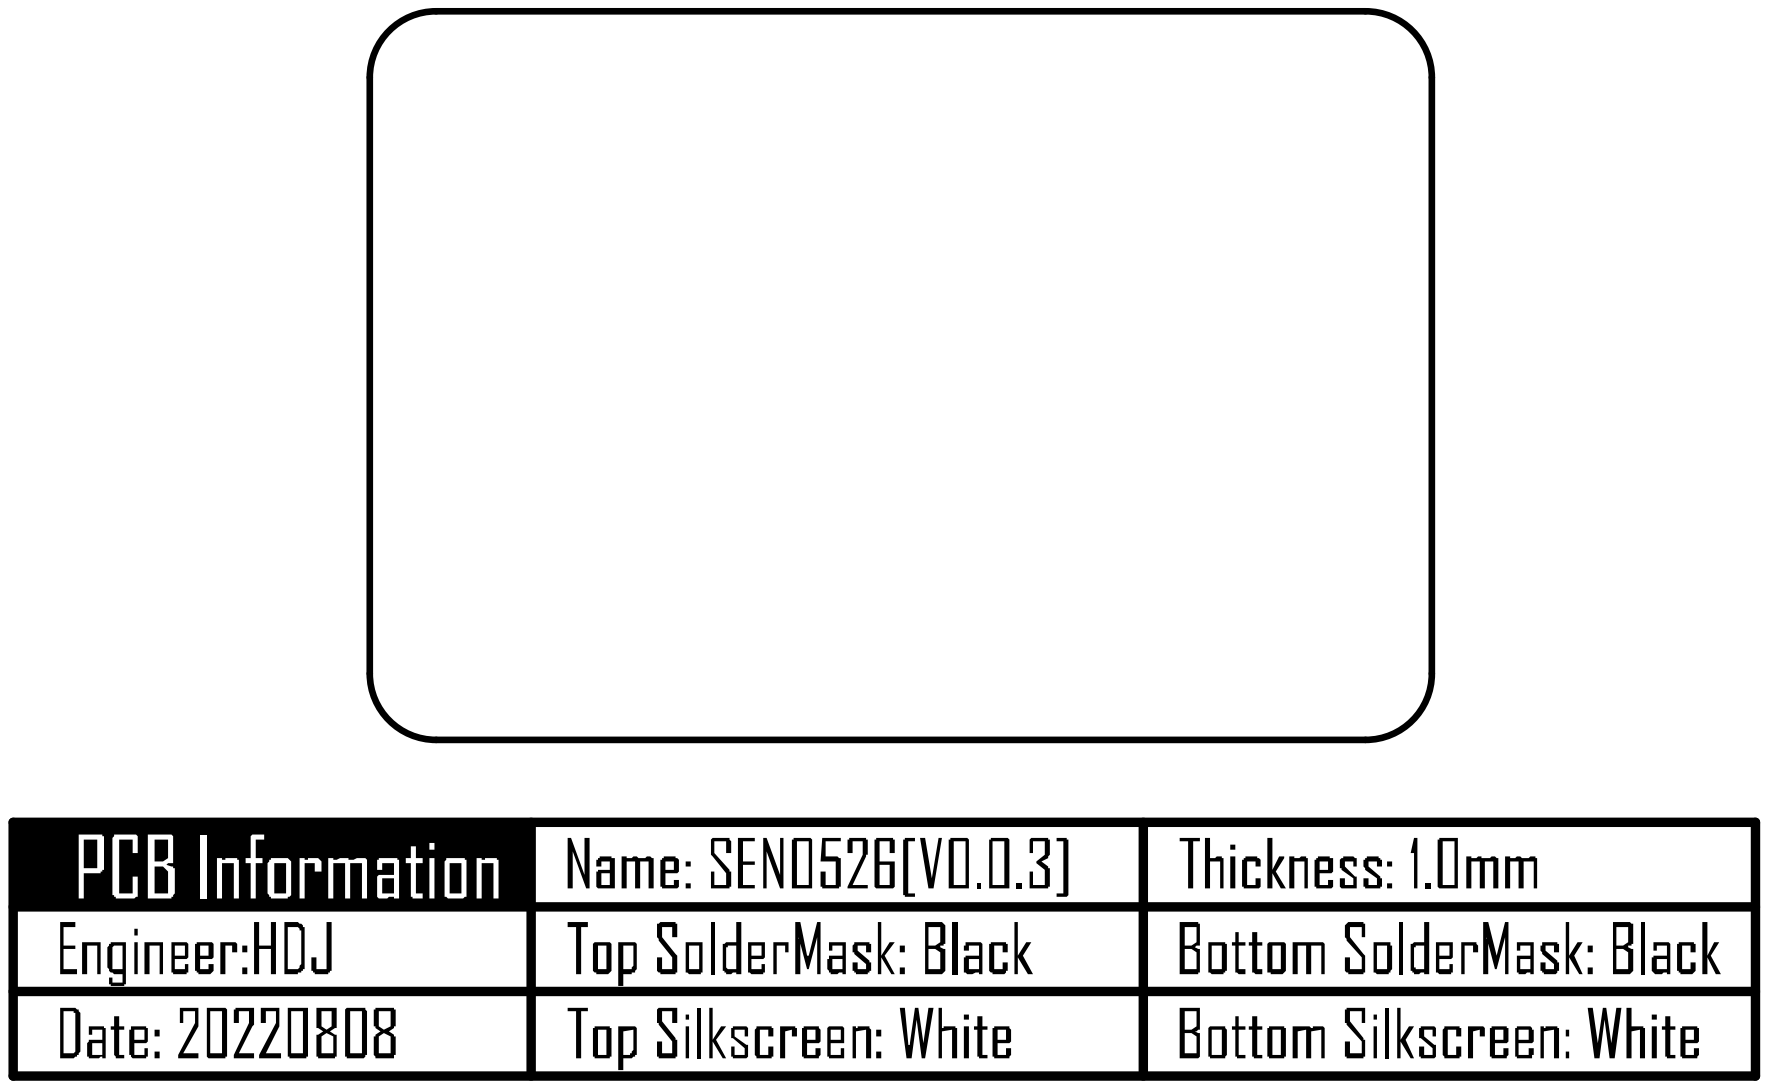
[picture p123: page 7]

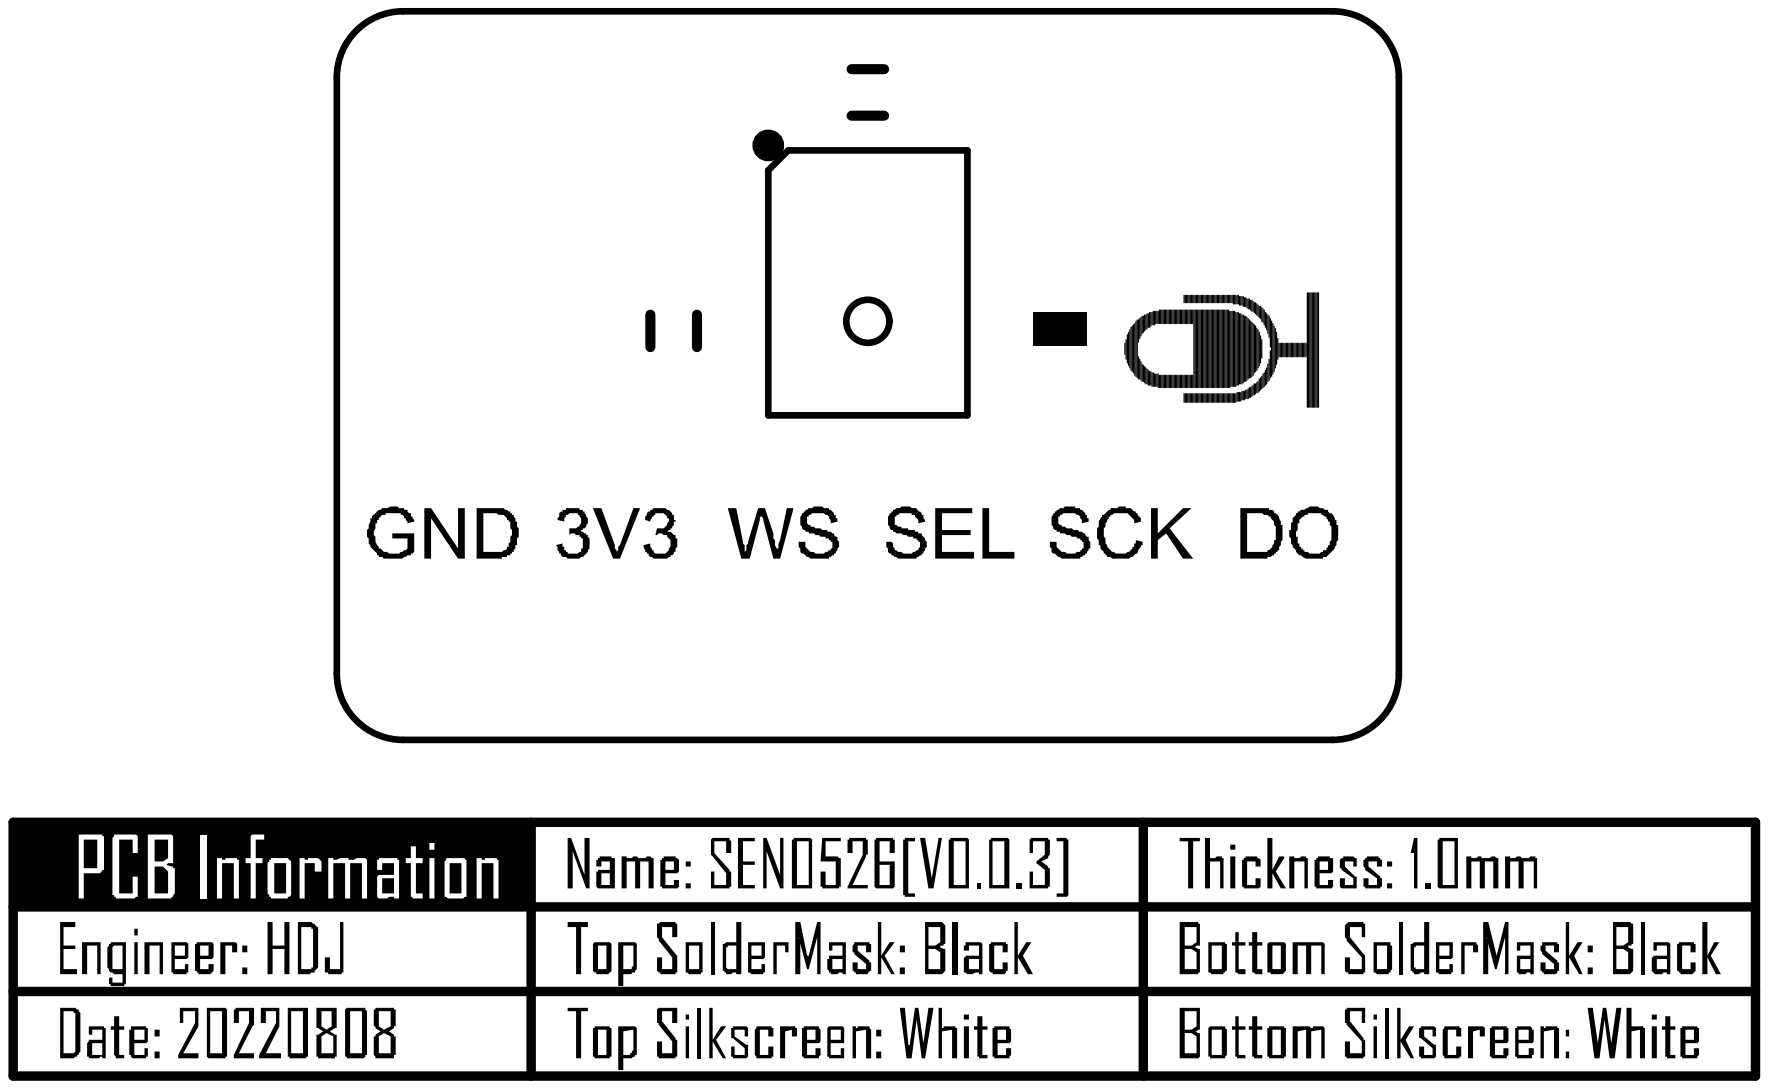
[picture p124: page 8]

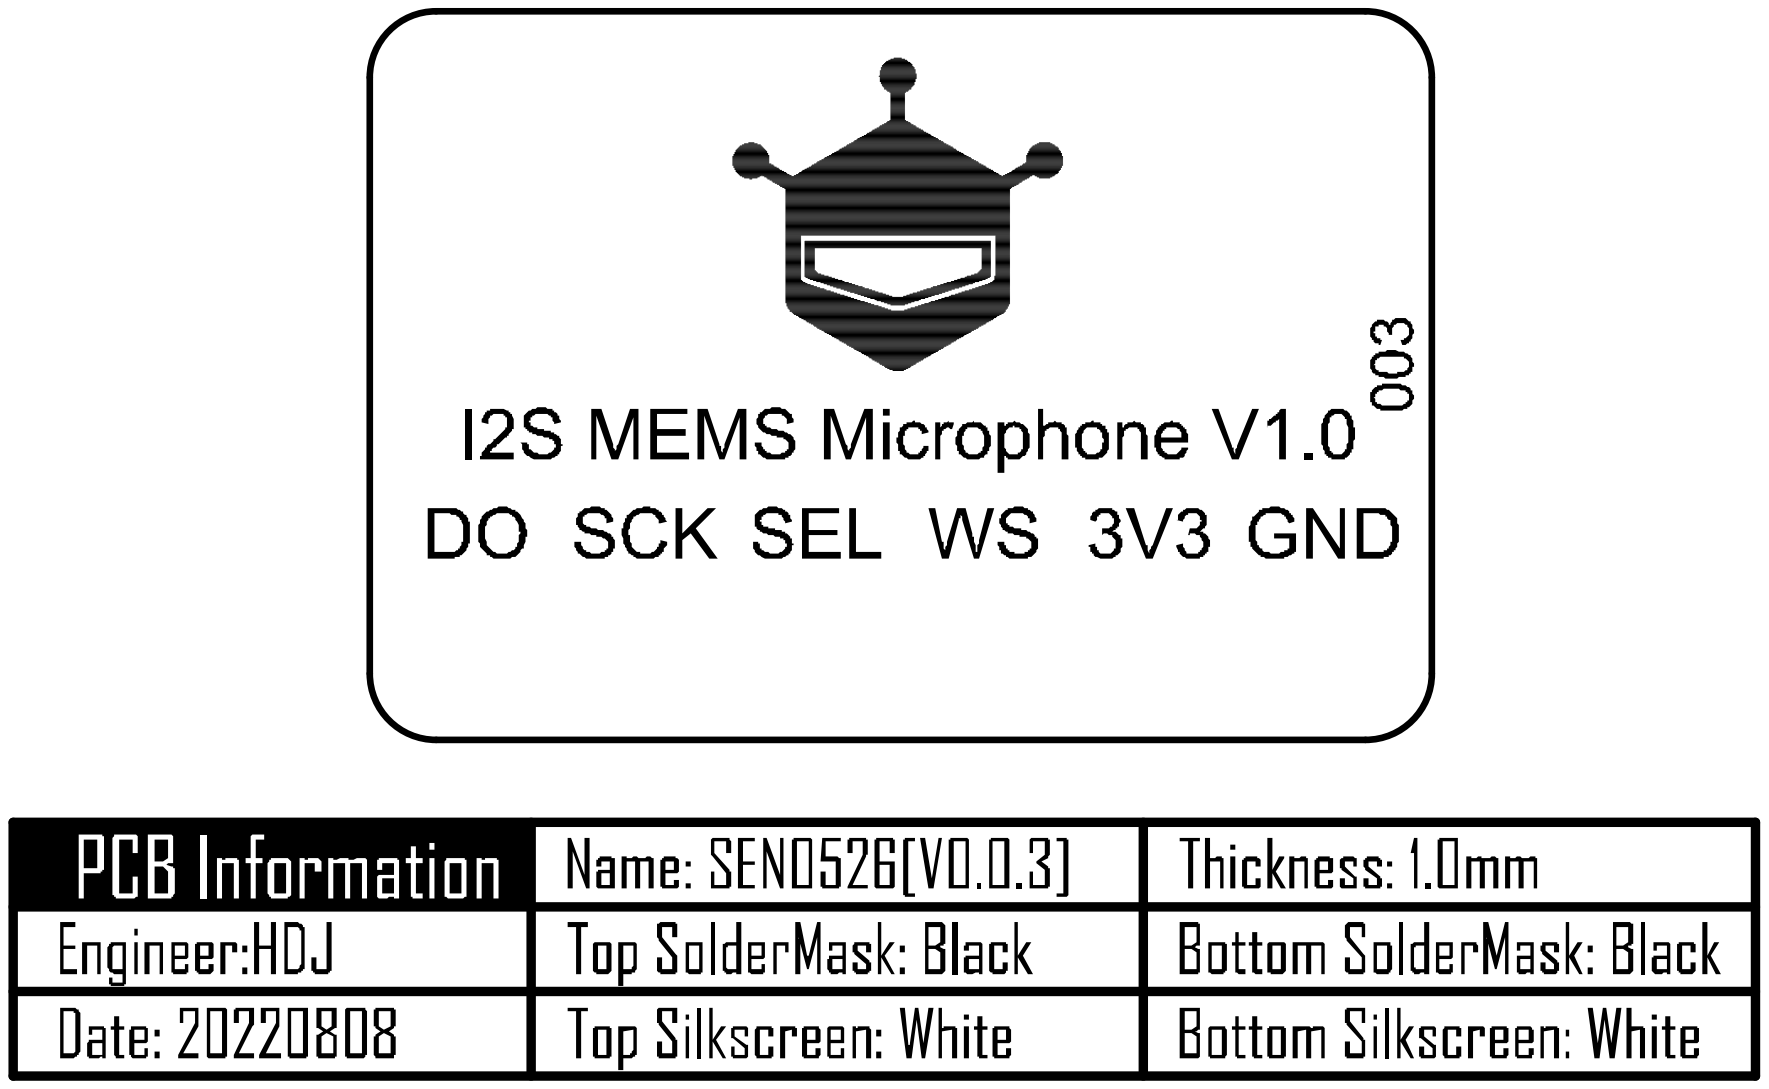
[picture p125: page 9]

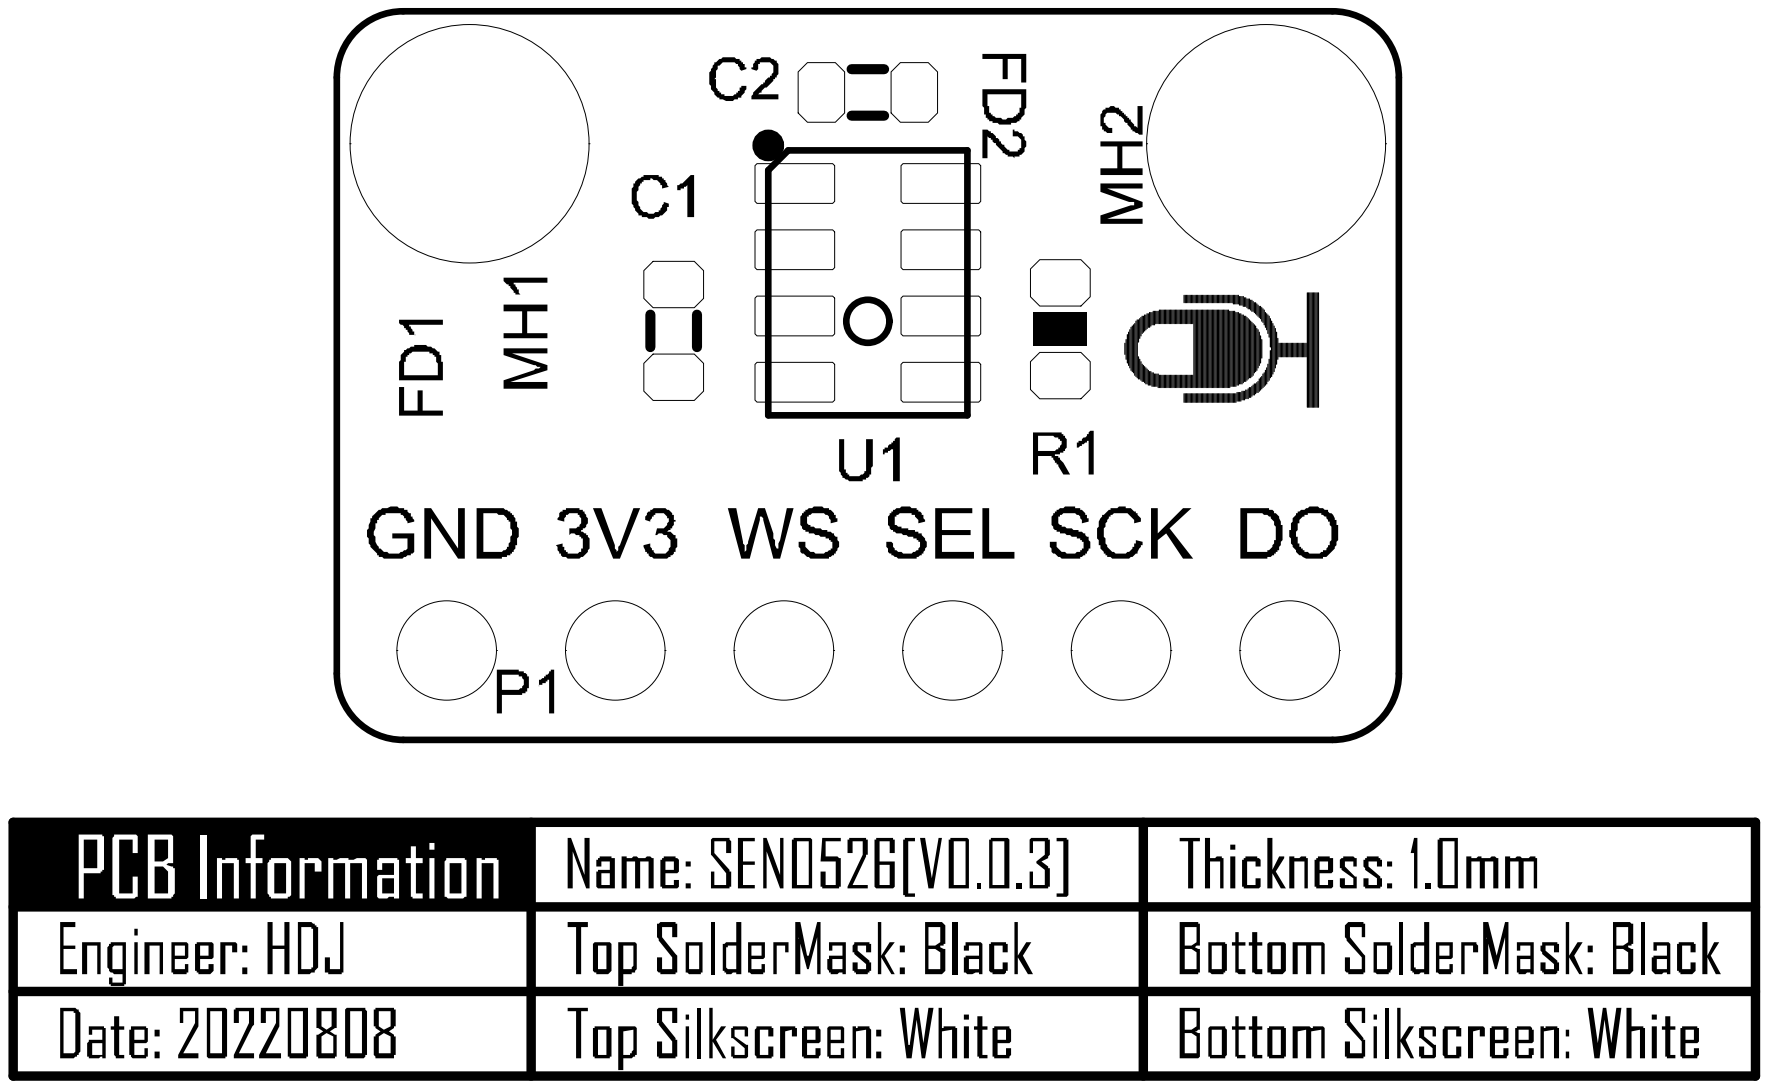
[picture p126: page 10]

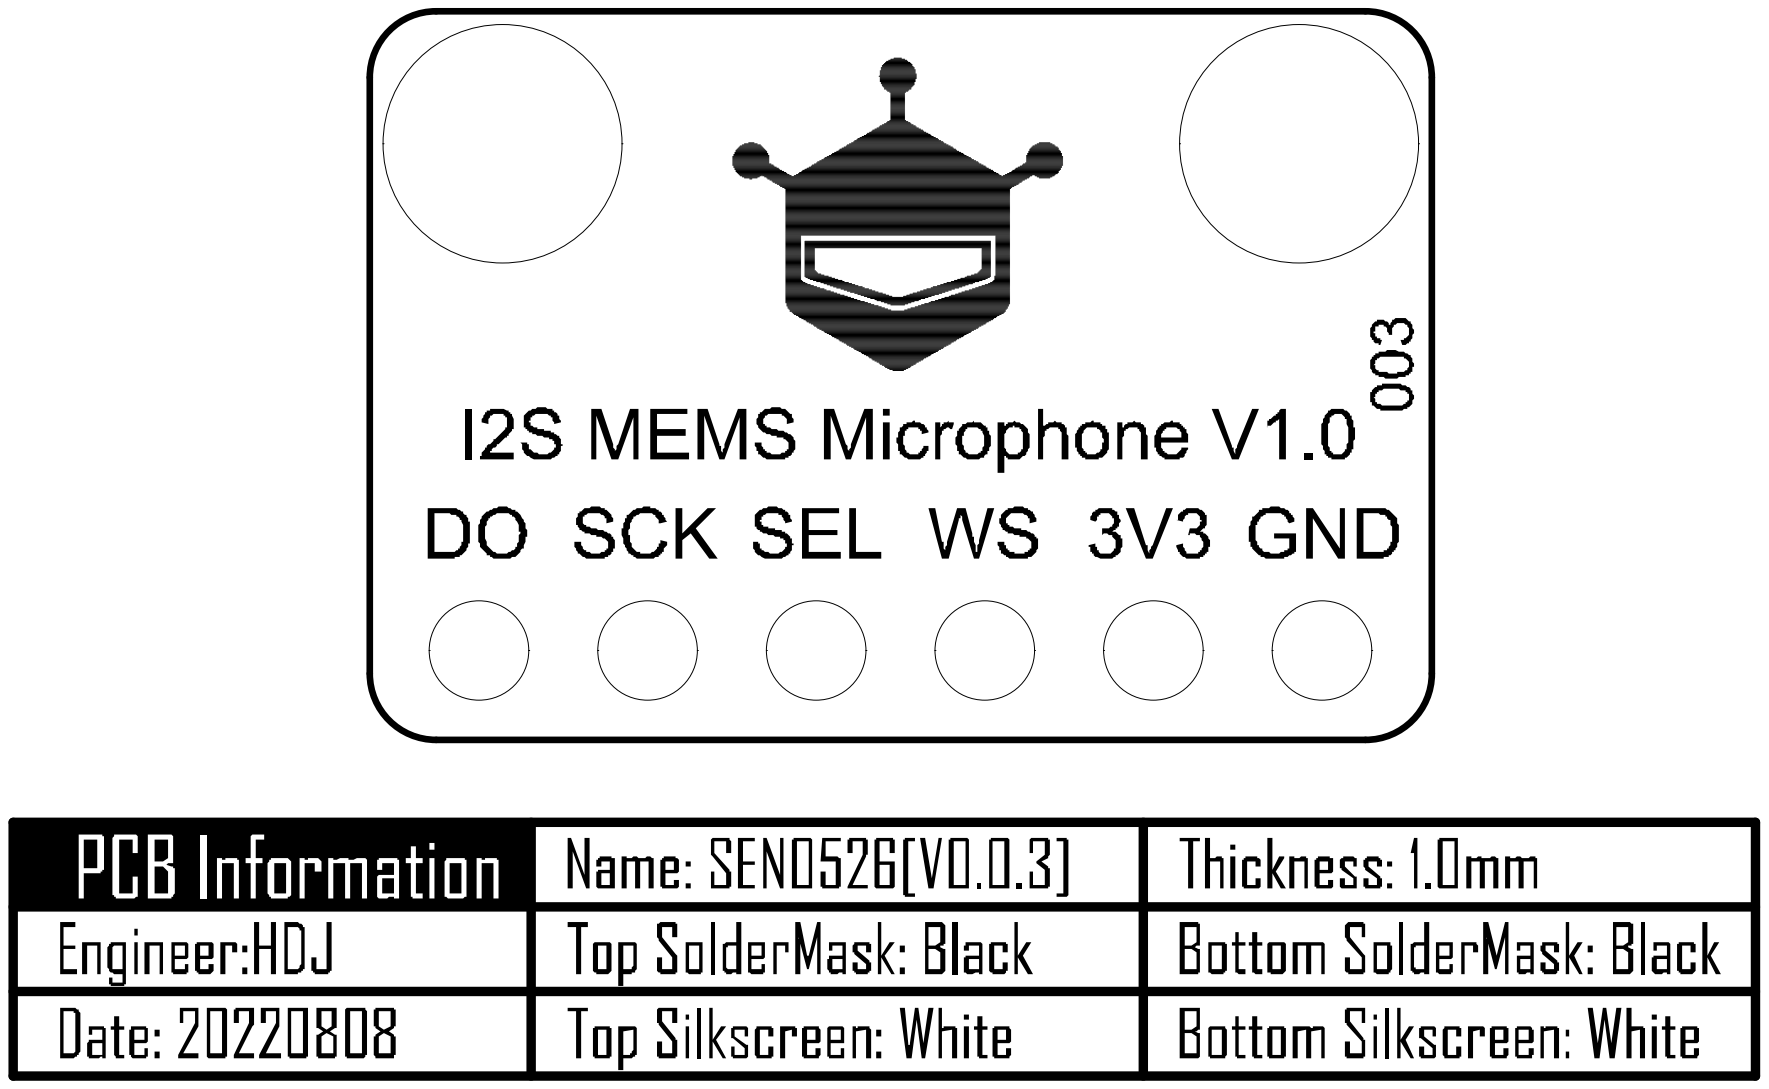
[picture p127: page 11]

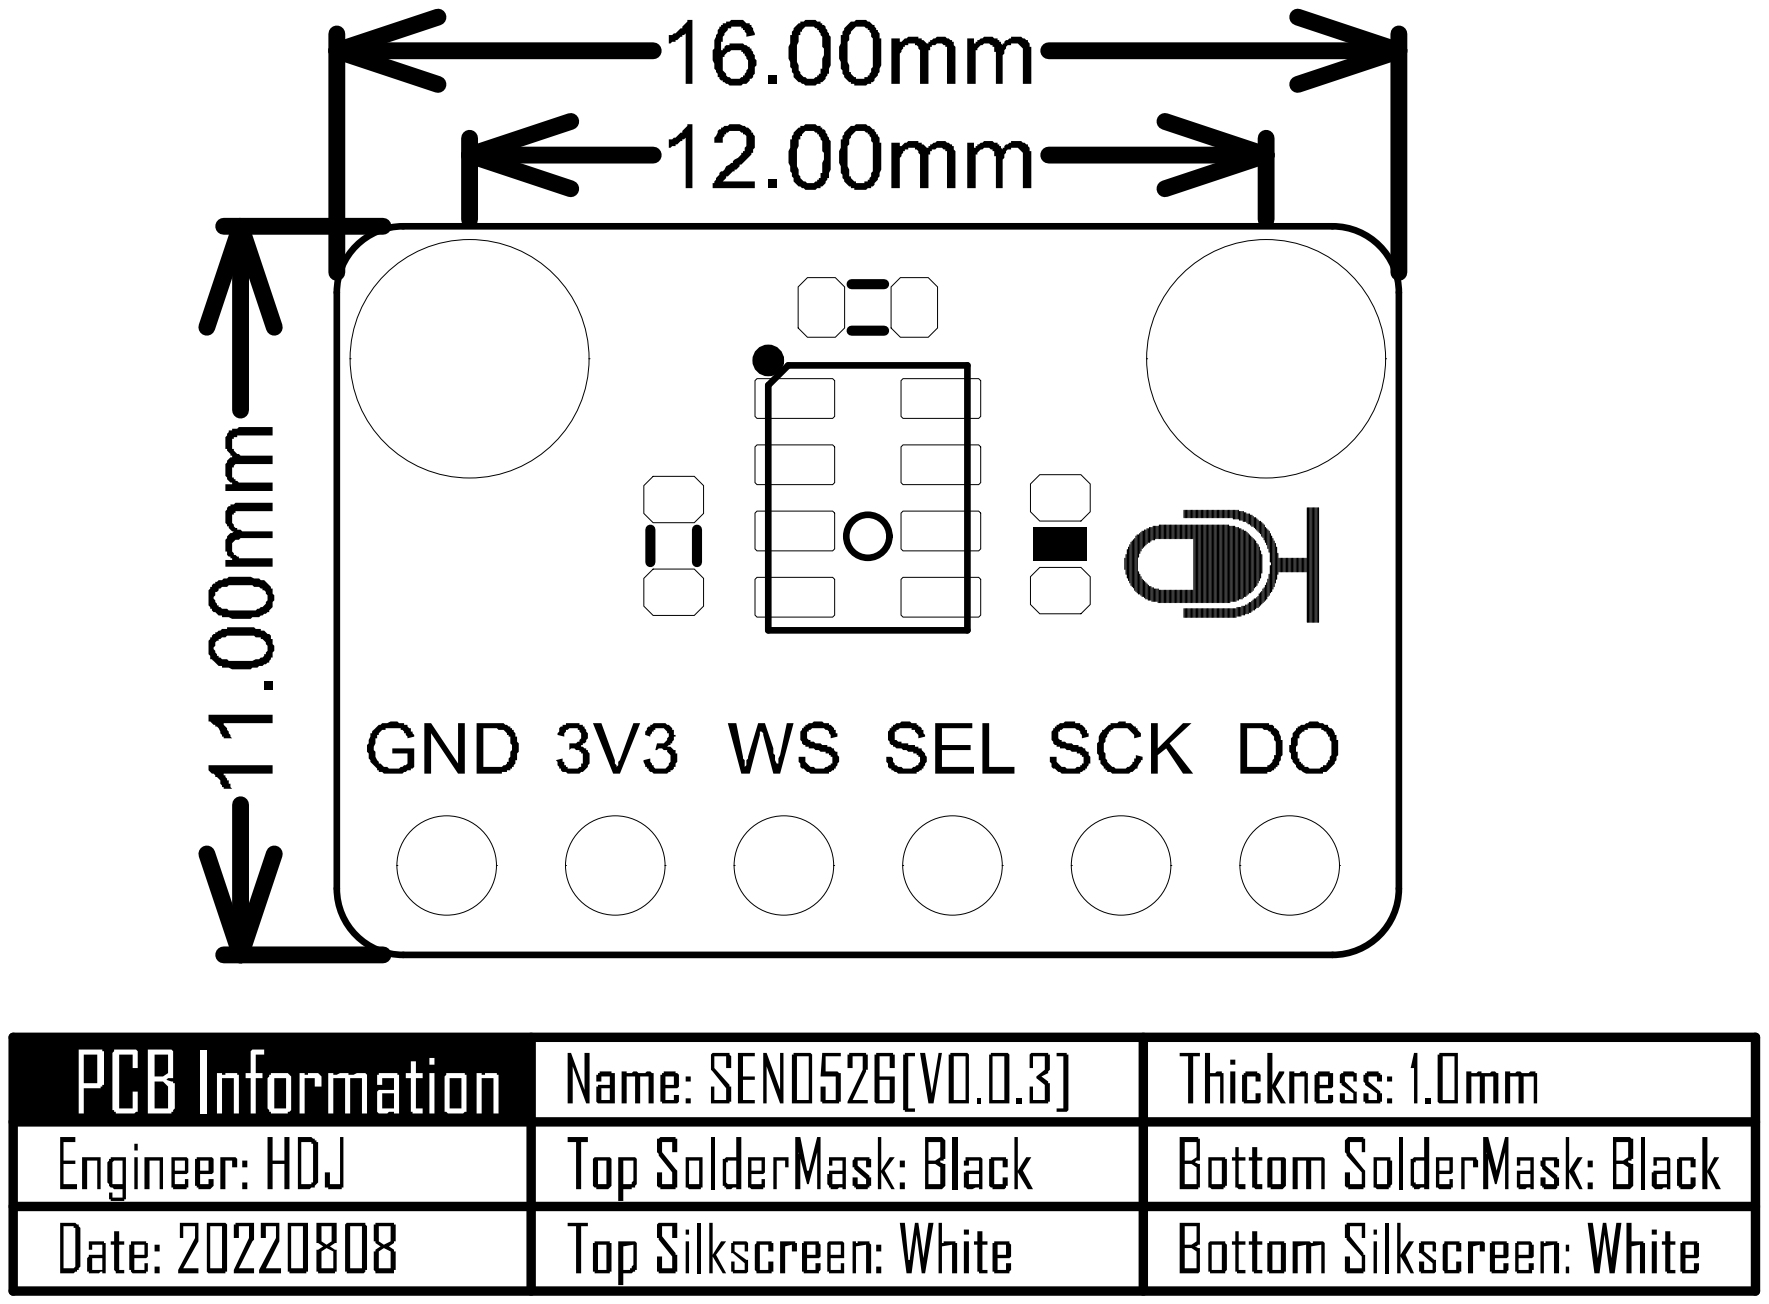
[picture p128: page 12]

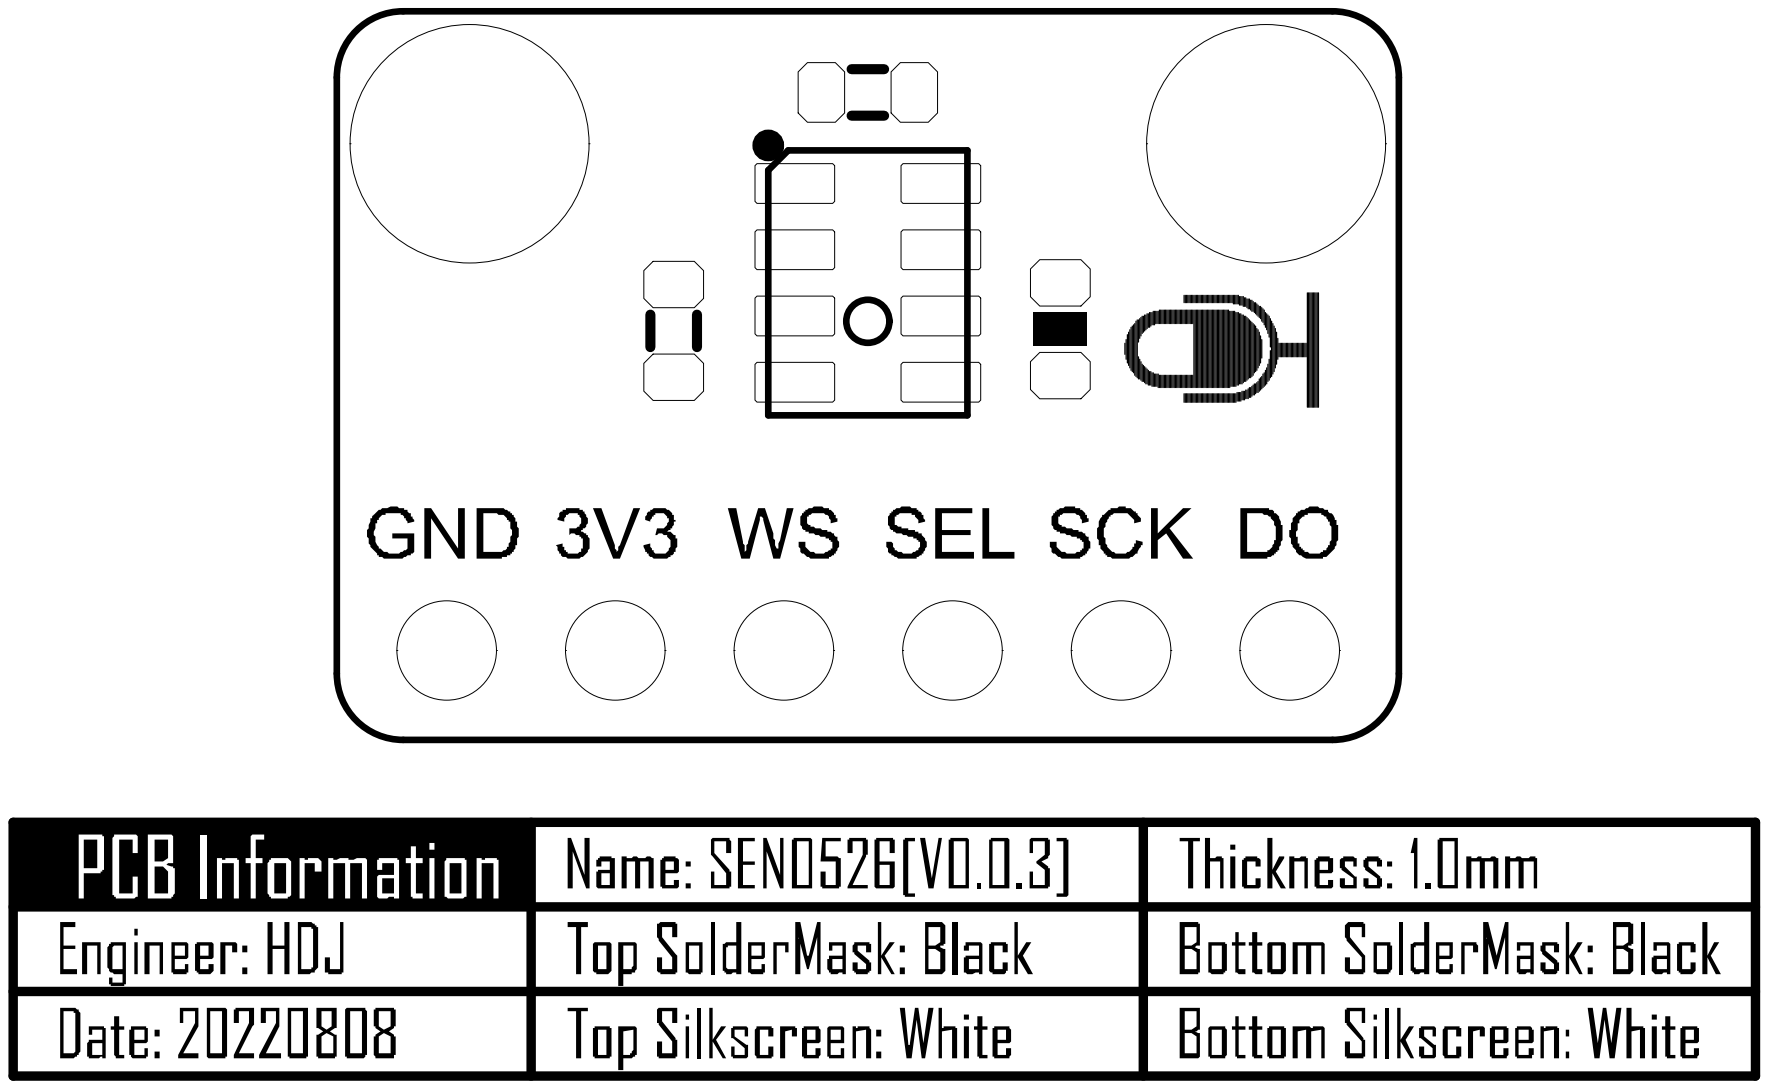
[picture p129: page 13]
