alnhan/WearableAlertDevice/Gunshot Detection Files/Old Microphone/I2S Microphone Resources/SEN0526_i2s-mems-microphone_dimension_v1.0.pdf

## Unit:mm

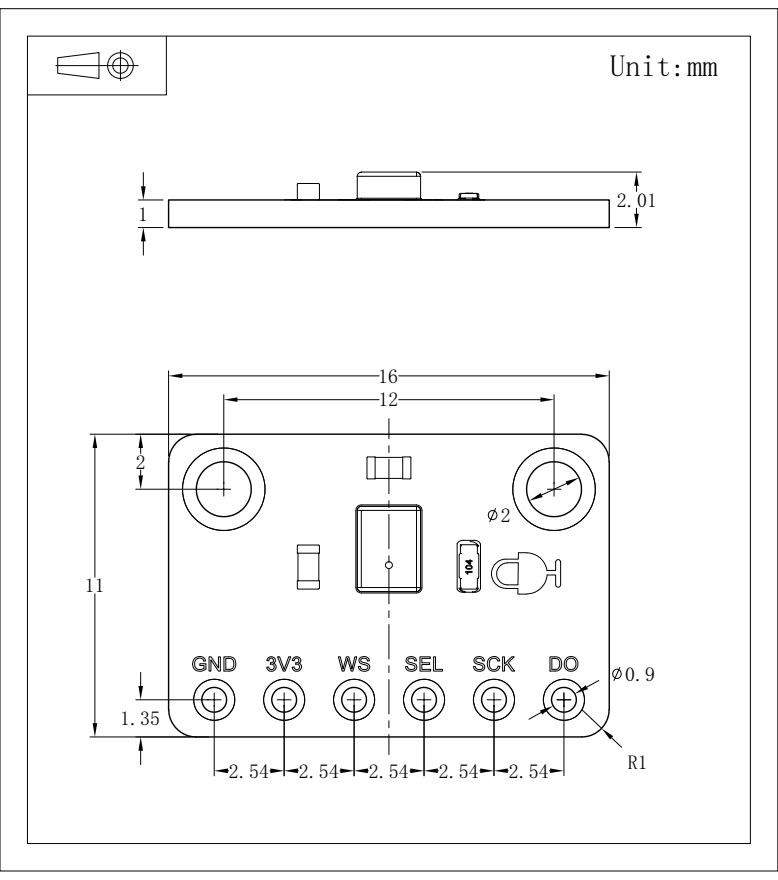
[picture p130: page 1]
