alnhan/WearableAlertDevice/KiCad Files/Wearable Alert Device Schematics/Old Design/GPS_System_Wiring.kicad_sch

## KiCad design KiCad Files/Wearable Alert Device Schematics/Old Design/GPS_System_Wiring.kicad_sch (2026-05-04, an earlier design)

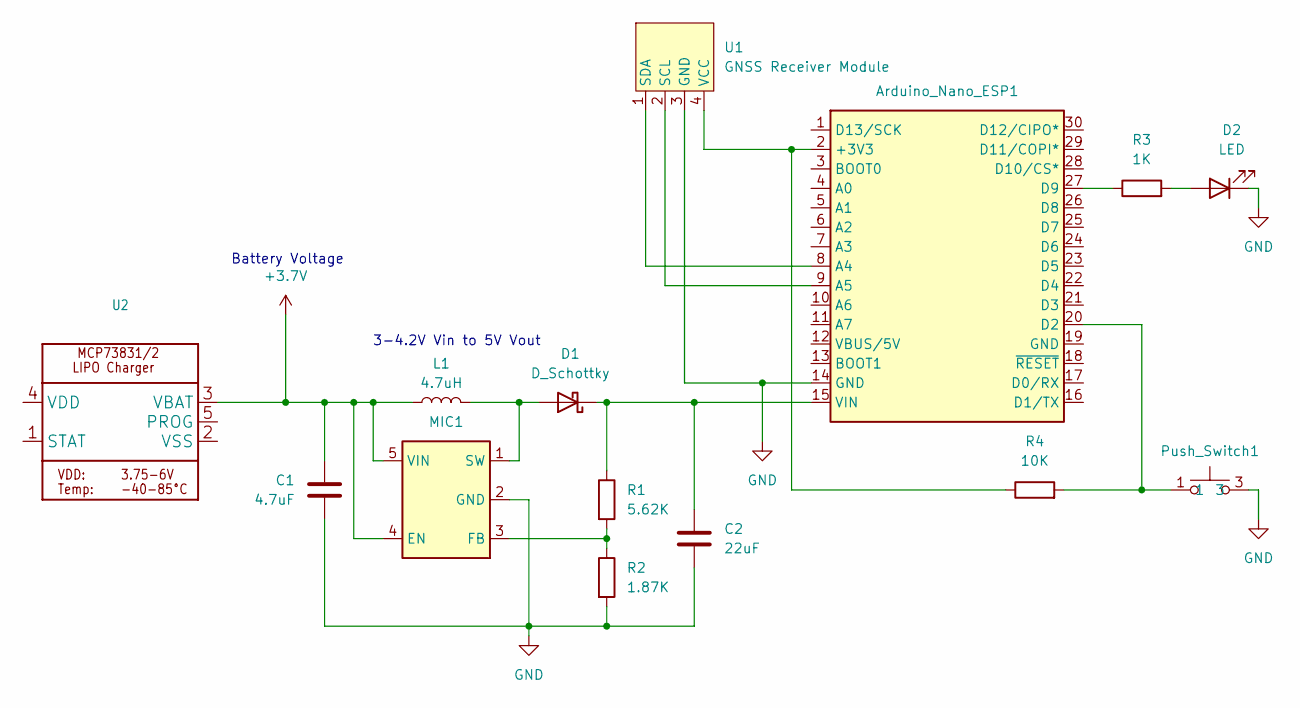
[picture p131: schematic GPS_System_Wiring.kicad_sch]

Parts:
Arduino_Nano_ESP1: (no value)
C1: 4.7uF
C2: 22uF
D1: D_Schottky
D2: LED
L1: 4.7uH
MIC1: (no value)
Push_Switch1: (no value)
R1: 5.62K
R2: 1.87K
R3: 1K
R4: 10K
U1: GNSS Receiver Module
U2: SOT23-5

Connections:
+3.7V: C1.2, L1.1, MIC1.4 (EN), MIC1.5 (VIN), U2.3 (VBAT)
GND: Arduino_Nano_ESP1.14 (GND), C1.1, C2.2, D2.1 (K), MIC1.2 (GND), Push_Switch1.3, R2.2, U1.3 (GND)
unnamed: Arduino_Nano_ESP1.2 (+3V3), R4.1, U1.4 (VCC)
unnamed: Arduino_Nano_ESP1.8 (A4), U1.1 (SDA)
unnamed: Arduino_Nano_ESP1.9 (A5), U1.2 (SCL)
unnamed: Arduino_Nano_ESP1.15 (VIN), C2.1, D1.1 (K), R1.1
unnamed: Arduino_Nano_ESP1.20 (D2), Push_Switch1.1, R4.2
unnamed: Arduino_Nano_ESP1.27 (D9), R3.1
unnamed: D1.2 (A), L1.2, MIC1.1 (SW)
unnamed: D2.2 (A), R3.2
unnamed: MIC1.3 (FB), R1.2, R2.1

Notes on the sheet:
Battery Voltage
3-4.2V Vin to 5V Vout
