alnhan/WearableAlertDevice/KiCad Files/Wearable Alert Device Schematics/WearableAlertDevice_Final/WearableAlertDevice_Final.kicad_sch

## KiCad design KiCad Files/Wearable Alert Device Schematics/WearableAlertDevice_Final/WearableAlertDevice_Final.kicad_sch (2026-05-04, an earlier design)

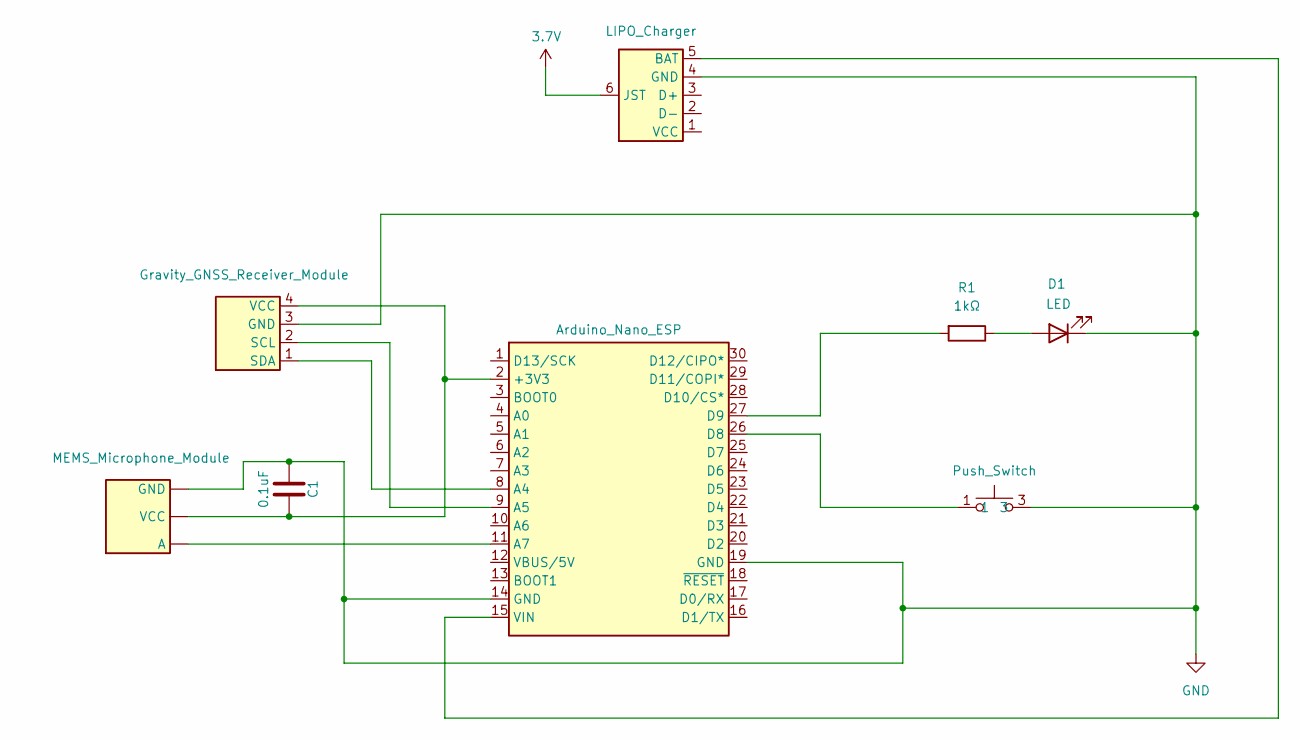
[picture p132: schematic WearableAlertDevice_Final.kicad_sch]

Parts:
Arduino_Nano_ESP: (no value)
C1: 0.1uF
D1: LED
Gravity_GNSS_Receiver_Module: (no value)
LIPO_Charger: (no value)
MEMS_Microphone_Module: (no value)
Push_Switch: (no value)
R1: 1kΩ

Connections:
3.7V: LIPO_Charger.6 (JST)
GND: Arduino_Nano_ESP.14 (GND), Arduino_Nano_ESP.19 (GND), C1.2, D1.1 (K), Gravity_GNSS_Receiver_Module.3 (GND), LIPO_Charger.4 (GND), MEMS_Microphone_Module., Push_Switch.3
unnamed: Arduino_Nano_ESP.2 (+3V3), C1.1, Gravity_GNSS_Receiver_Module.4 (VCC), MEMS_Microphone_Module.
unnamed: Arduino_Nano_ESP.8 (A4), Gravity_GNSS_Receiver_Module.1 (SDA)
unnamed: Arduino_Nano_ESP.9 (A5), Gravity_GNSS_Receiver_Module.2 (SCL)
unnamed: Arduino_Nano_ESP.11 (A7), MEMS_Microphone_Module.
unnamed: Arduino_Nano_ESP.15 (VIN), LIPO_Charger.5 (BAT)
unnamed: Arduino_Nano_ESP.26 (D8), Push_Switch.1
unnamed: Arduino_Nano_ESP.27 (D9), R1.2
unnamed: D1.2 (A), R1.1
