alnhan/WearableAlertDevice/KiCad Files/Wearable Alert Device Schematics/WearableAlertDevice_Wiring_Diagram_Final/WearableAlertDevice_Wiring_Diagram_Final.kicad_sch

## KiCad design KiCad Files/Wearable Alert Device Schematics/WearableAlertDevice_Wiring_Diagram_Final/WearableAlertDevice_Wiring_Diagram_Final.kicad_sch (2026-05-04, an earlier design)

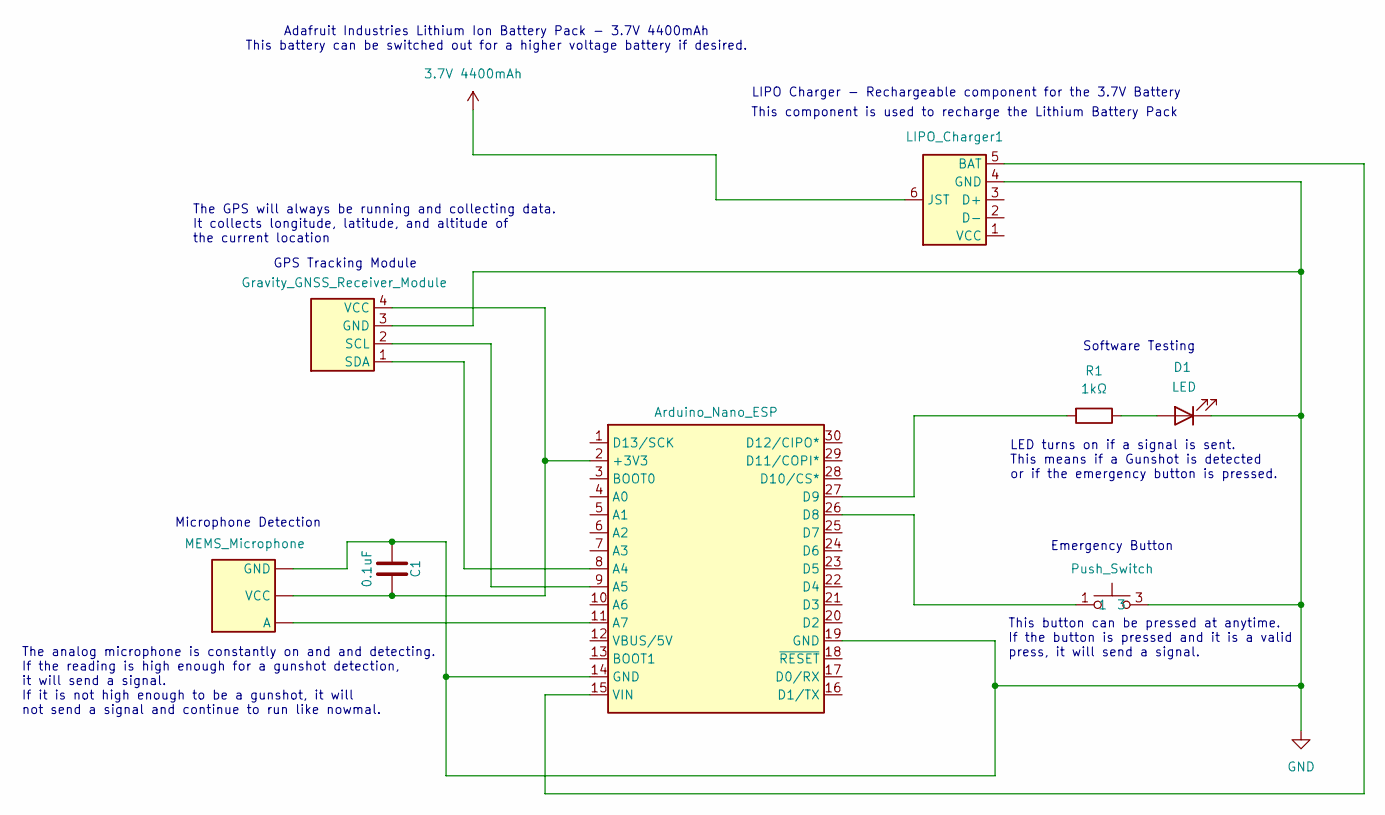
[picture p133: schematic WearableAlertDevice_Wiring_Diagram_Final.kicad_sch]

Parts:
Arduino_Nano_ESP: (no value)
C1: 0.1uF
D1: LED
Gravity_GNSS_Receiver_Module: (no value)
LIPO_Charger1: (no value)
MEMS_Microphone: (no value)
Push_Switch: (no value)
R1: 1kΩ

Connections:
3.7V 4400mAh: LIPO_Charger1.6 (JST)
GND: Arduino_Nano_ESP.14 (GND), Arduino_Nano_ESP.19 (GND), C1.2, D1.1 (K), Gravity_GNSS_Receiver_Module.3 (GND), LIPO_Charger1.4 (GND), MEMS_Microphone., Push_Switch.3
unnamed: Arduino_Nano_ESP.2 (+3V3), C1.1, Gravity_GNSS_Receiver_Module.4 (VCC), MEMS_Microphone.
unnamed: Arduino_Nano_ESP.8 (A4), Gravity_GNSS_Receiver_Module.1 (SDA)
unnamed: Arduino_Nano_ESP.9 (A5), Gravity_GNSS_Receiver_Module.2 (SCL)
unnamed: Arduino_Nano_ESP.11 (A7), MEMS_Microphone.
unnamed: Arduino_Nano_ESP.15 (VIN), LIPO_Charger1.5 (BAT)
unnamed: Arduino_Nano_ESP.26 (D8), Push_Switch.1
unnamed: Arduino_Nano_ESP.27 (D9), R1.2
unnamed: D1.2 (A), R1.1

Notes on the sheet:
Software Testing
Microphone Detection
The GPS will always be running and collecting data. It collects longitude, latitude, and altitude of the current location
Adafruit Industries Lithium Ion Battery Pack - 3.7V 4400mAh This battery can be switched out for a higher voltage battery if desired.
LIPO Charger - Rechargeable component for the 3.7V Battery
This button can be pressed at anytime. If the button is pressed and it is a valid press, it will send a signal.
GPS Tracking Module
Emergency Button
This component is used to recharge the Lithium Battery Pack
LED turns on if a signal is sent. This means if a Gunshot is detected or if the emergency button is pressed.
The analog microphone is constantly on and and detecting. If the reading is high enough for a gunshot detection, it will send a signal. If it is not high enough to be a gunshot, it will not send a signal and continue to run like nowmal.
