alnhan/WearableAlertDevice/KiCad Files/Wearable Alert Device Schematics/Old Design/Wearable_Alert_Device/Wearable_Alert_Device.kicad_sch

## KiCad design KiCad Files/Wearable Alert Device Schematics/Old Design/Wearable_Alert_Device/Wearable_Alert_Device.kicad_sch (2026-05-04, an earlier design)

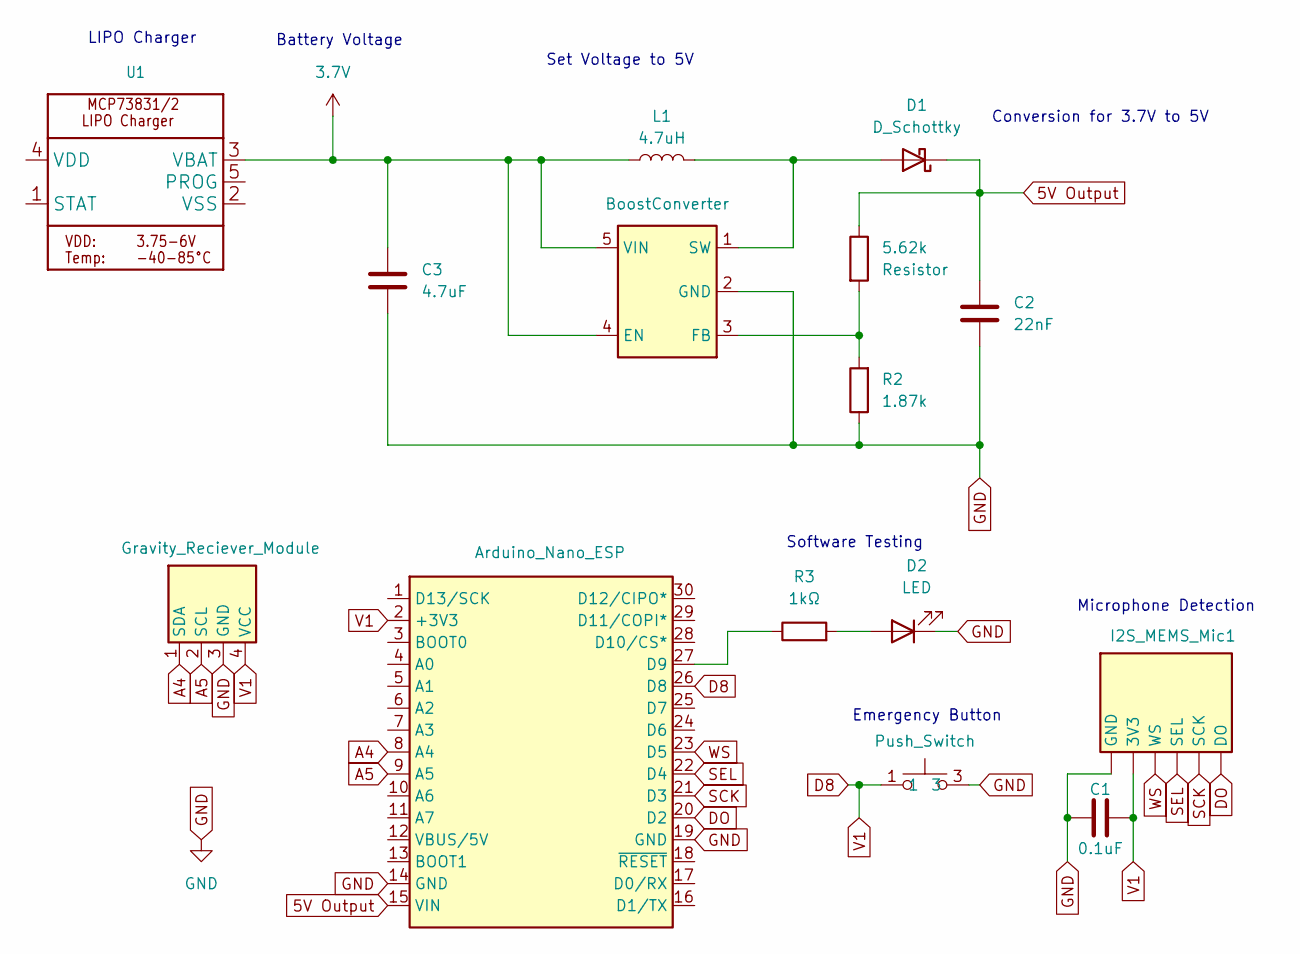
[picture p136: schematic Wearable_Alert_Device.kicad_sch]

Parts:
5.62k: Resistor
Arduino_Nano_ESP: (no value)
BoostConverter: (no value)
C1: 0.1uF
C2: 22nF
C3: 4.7uF
D1: D_Schottky
D2: LED
Gravity_Reciever_Module: (no value)
I2S_MEMS_Mic1: (no value)
L1: 4.7uH
Push_Switch: (no value)
R2: 1.87k
R3: 1kΩ
U1: SOT23-5

Connections:
3.7V: BoostConverter.4 (EN), BoostConverter.5 (VIN), C3.1, L1.1, U1.3 (VBAT)
5V Output: 5.62k.1, Arduino_Nano_ESP.15 (VIN), C2.1, D1.1 (K)
A4: Arduino_Nano_ESP.8 (A4), Gravity_Reciever_Module.1 (SDA)
A5: Arduino_Nano_ESP.9 (A5), Gravity_Reciever_Module.2 (SCL)
D8: Arduino_Nano_ESP.2 (+3V3), Arduino_Nano_ESP.26 (D8), C1.1, Gravity_Reciever_Module.4 (VCC), I2S_MEMS_Mic1., Push_Switch.1
DO: Arduino_Nano_ESP.20 (D2), I2S_MEMS_Mic1.
GND: Arduino_Nano_ESP.14 (GND), Arduino_Nano_ESP.19 (GND), BoostConverter.2 (GND), C1.2, C2.2, C3.2, D2.1 (K), Gravity_Reciever_Module.3 (GND), I2S_MEMS_Mic1., Push_Switch.3, R2.1
unnamed: 5.62k.2, BoostConverter.3 (FB), R2.2
unnamed: Arduino_Nano_ESP.27 (D9), R3.1
unnamed: BoostConverter.1 (SW), D1.2 (A), L1.2
unnamed: D2.2 (A), R3.2
SCK: Arduino_Nano_ESP.21 (D3), I2S_MEMS_Mic1.
SEL: Arduino_Nano_ESP.22 (D4), I2S_MEMS_Mic1.
WS: Arduino_Nano_ESP.23 (D5), I2S_MEMS_Mic1.

Notes on the sheet:
Emergency Button
Microphone Detection
Set Voltage to 5V
LIPO Charger
Conversion for 3.7V to 5V
Battery Voltage
Software Testing
