alnhan/WearableAlertDevice/KiCad Files/Wearable Alert Device Schematics/Old Design/Wearable_Alert_Device_Wiring/Wearable_Alert_Device_Wiring.kicad_sch

## KiCad design KiCad Files/Wearable Alert Device Schematics/Old Design/Wearable_Alert_Device_Wiring/Wearable_Alert_Device_Wiring.kicad_sch (2026-05-04, an earlier design)

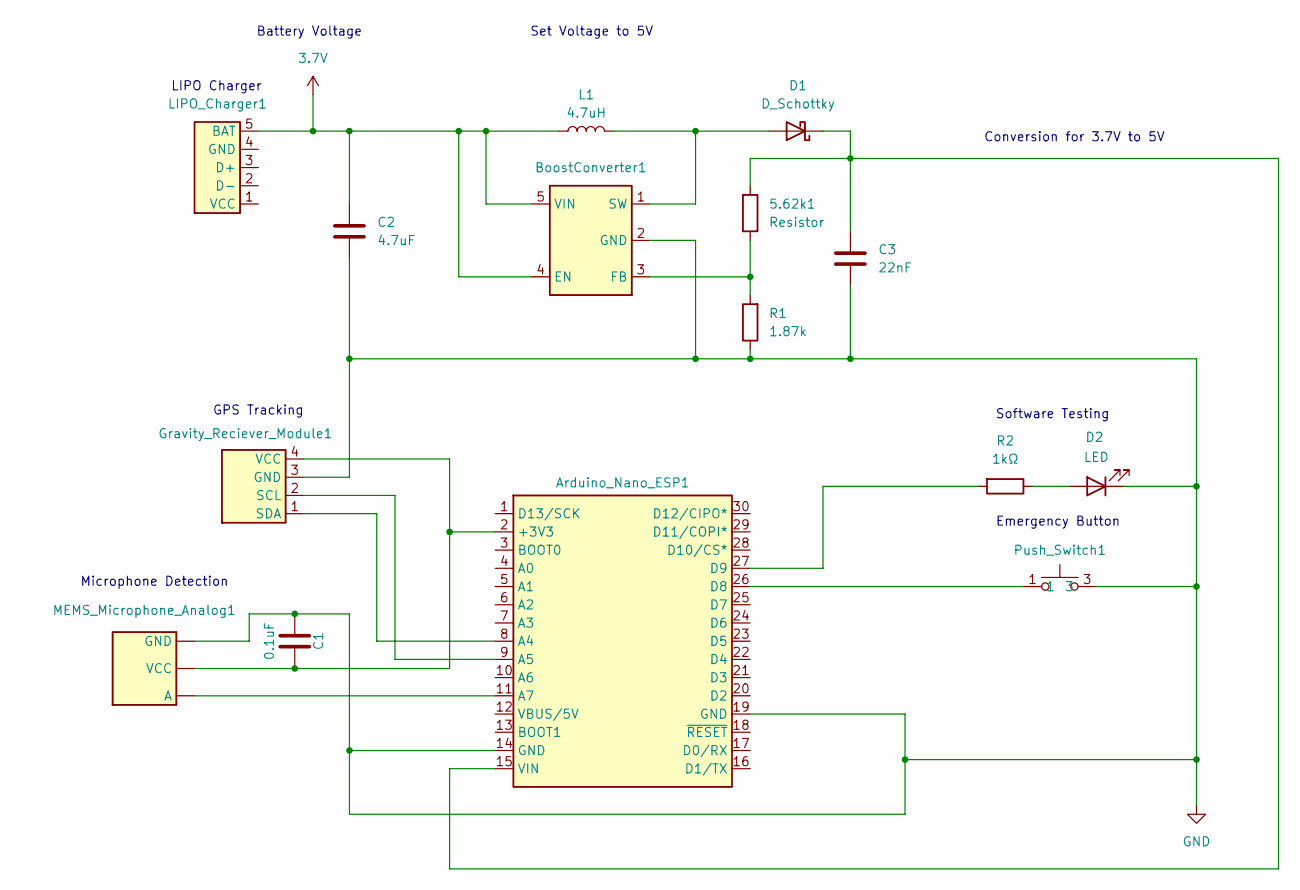
[picture p137: schematic Wearable_Alert_Device_Wiring.kicad_sch]

Parts:
5.62k1: Resistor
Arduino_Nano_ESP1: (no value)
BoostConverter1: (no value)
C1: 0.1uF
C2: 4.7uF
C3: 22nF
D1: D_Schottky
D2: LED
Gravity_Reciever_Module1: (no value)
L1: 4.7uH
LIPO_Charger1: (no value)
MEMS_Microphone_Analog1: (no value)
Push_Switch1: (no value)
R1: 1.87k
R2: 1kΩ

Connections:
3.7V: BoostConverter1.4 (EN), BoostConverter1.5 (VIN), C2.1, L1.1, LIPO_Charger1.5 (BAT)
GND: Arduino_Nano_ESP1.14 (GND), Arduino_Nano_ESP1.19 (GND), BoostConverter1.2 (GND), C1.2, C2.2, C3.2, D2.1 (K), Gravity_Reciever_Module1.3 (GND), MEMS_Microphone_Analog1., Push_Switch1.3, R1.1
unnamed: 5.62k1.1, Arduino_Nano_ESP1.15 (VIN), C3.1, D1.1 (K)
unnamed: 5.62k1.2, BoostConverter1.3 (FB), R1.2
unnamed: Arduino_Nano_ESP1.2 (+3V3), C1.1, Gravity_Reciever_Module1.4 (VCC), MEMS_Microphone_Analog1.
unnamed: Arduino_Nano_ESP1.8 (A4), Gravity_Reciever_Module1.1 (SDA)
unnamed: Arduino_Nano_ESP1.9 (A5), Gravity_Reciever_Module1.2 (SCL)
unnamed: Arduino_Nano_ESP1.11 (A7), MEMS_Microphone_Analog1.
unnamed: Arduino_Nano_ESP1.26 (D8), Push_Switch1.1
unnamed: Arduino_Nano_ESP1.27 (D9), R2.2
unnamed: BoostConverter1.1 (SW), D1.2 (A), L1.2
unnamed: D2.2 (A), R2.1

Notes on the sheet:
Battery Voltage
GPS Tracking
Emergency Button
Conversion for 3.7V to 5V
Software Testing
Set Voltage to 5V
Microphone Detection
LIPO Charger
